peterantypas/maiana/images/Antenna-Example1.jpg

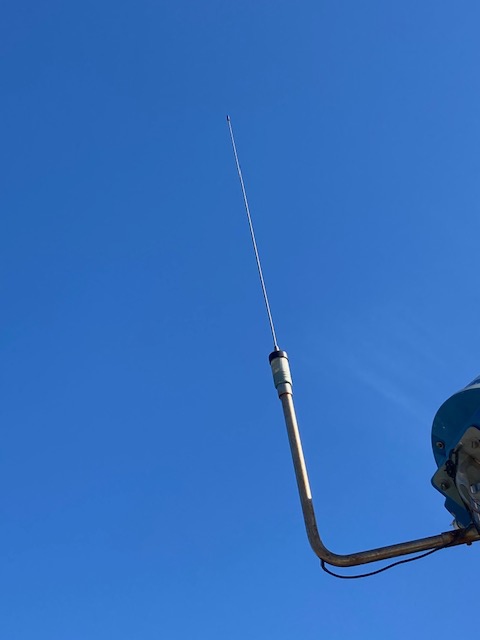
images/Antenna-Example1.jpg
