peterantypas/maiana/images/Antenna-Example3.jpg

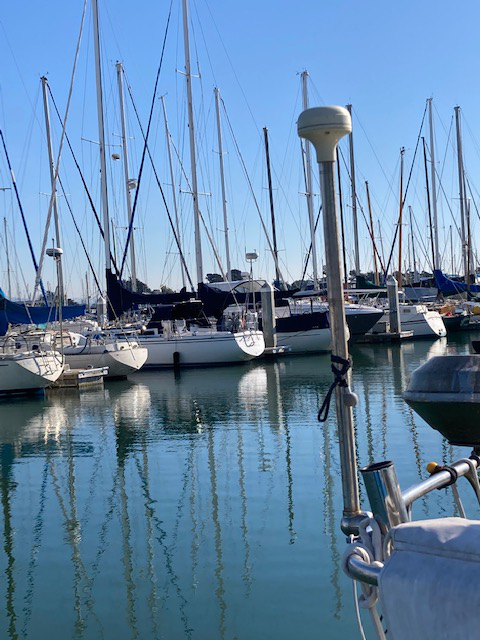
images/Antenna-Example3.jpg
