peterantypas/maiana/images/Board4.3.jpg

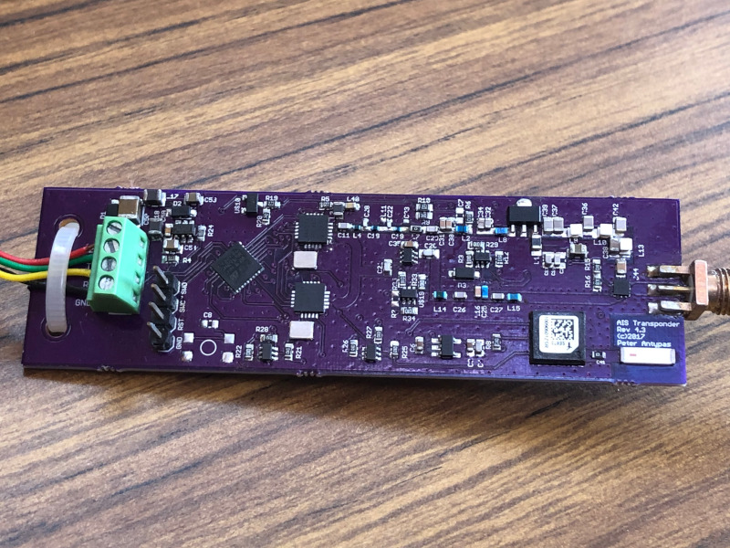
images/Board4.3.jpg
