peterantypas/maiana/images/board-11.3.0.jpg

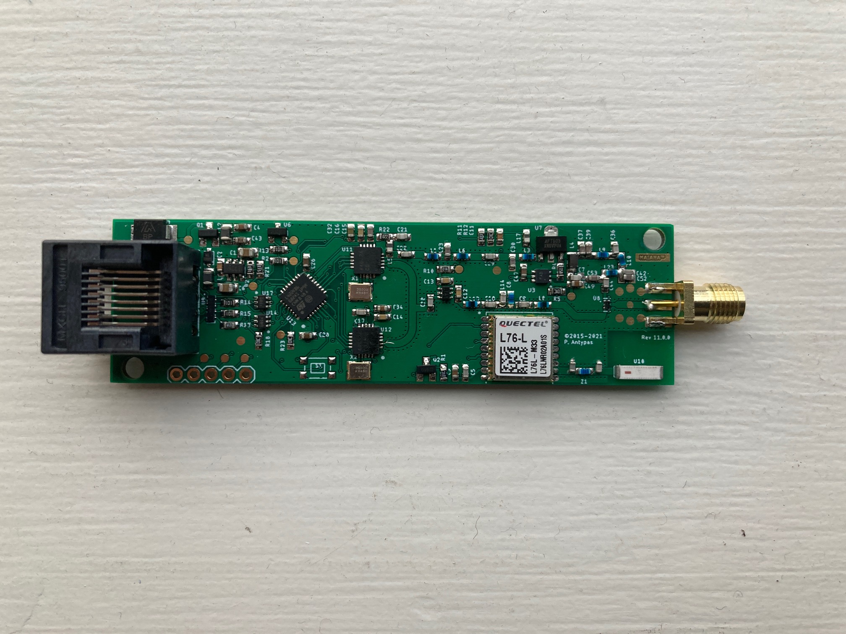
images/board-11.3.0.jpg
