peterantypas/maiana/images/transponder-6.1.jpg

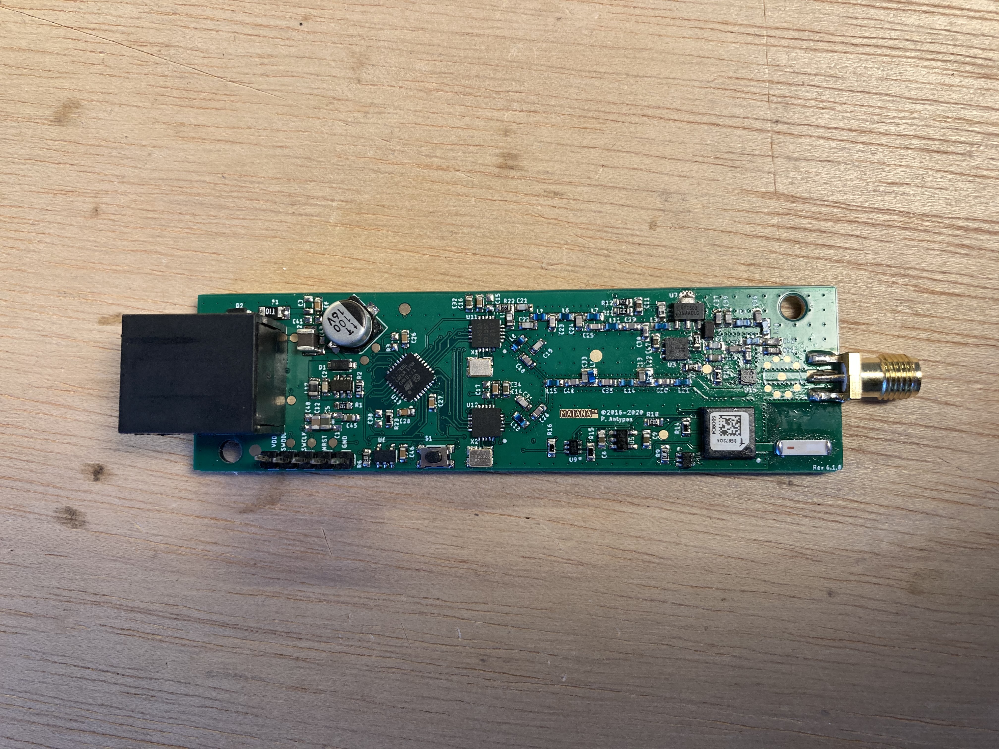
images/transponder-6.1.jpg
