peterantypas/maiana/images/transponder-9.3.jpg

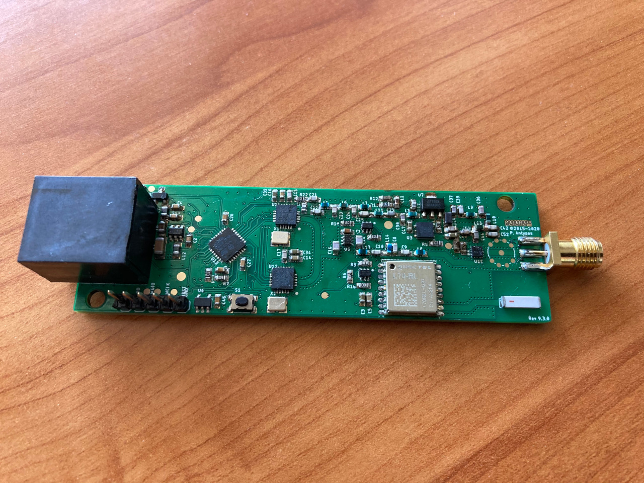
images/transponder-9.3.jpg
