peterantypas/maiana/images/uart_breakout.jpg

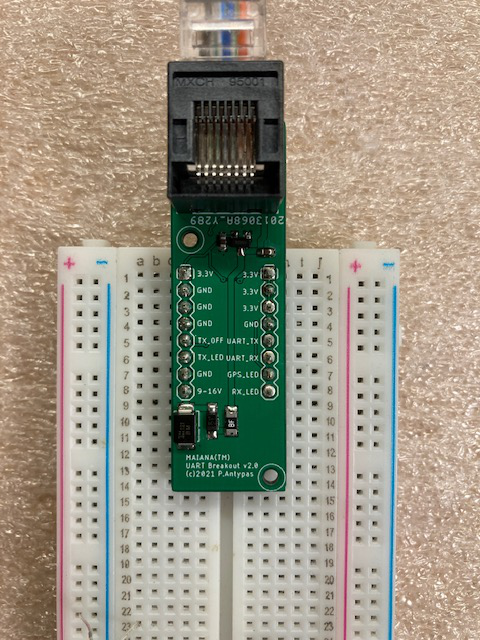
images/uart_breakout.jpg
