peterantypas/maiana/images/usbadapter.jpg

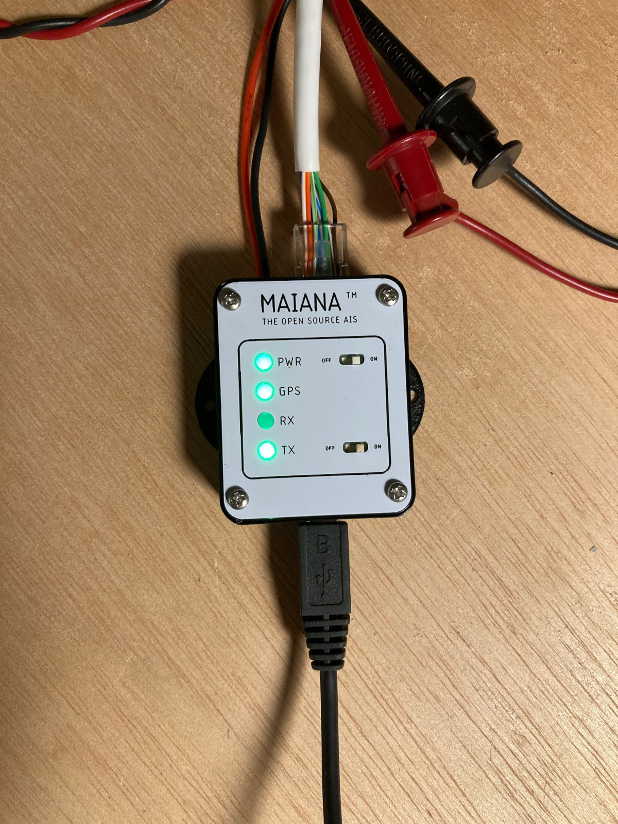
images/usbadapter.jpg
