peterantypas/maiana/latest/CAD/NMEA2000Breakout/n2k-breakout-3.0-ISO-GreenPAK.png

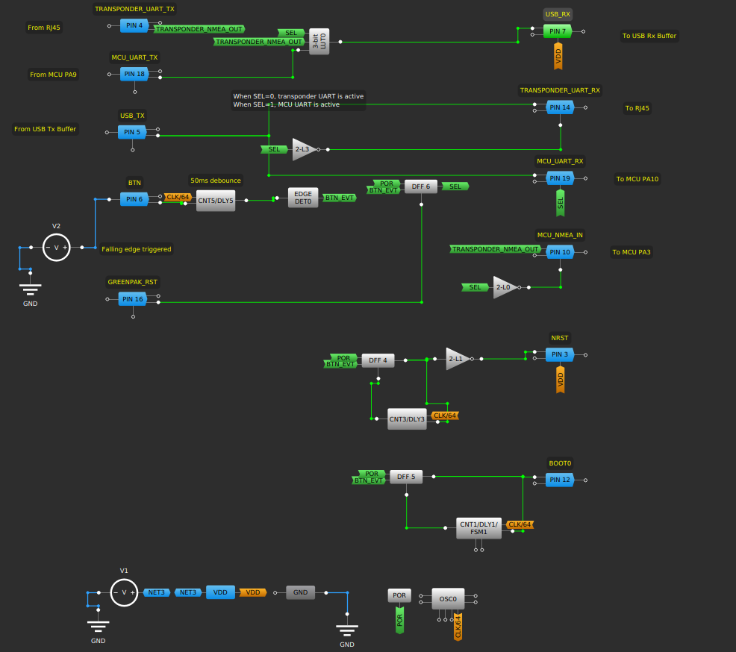
latest/CAD/NMEA2000Breakout/n2k-breakout-3.0-ISO-GreenPAK.png
