peterantypas/maiana/latest/CAD/NMEA2000Breakout/Rev8.1/NMEA2000Adapter-8.1-Schematic.pdf

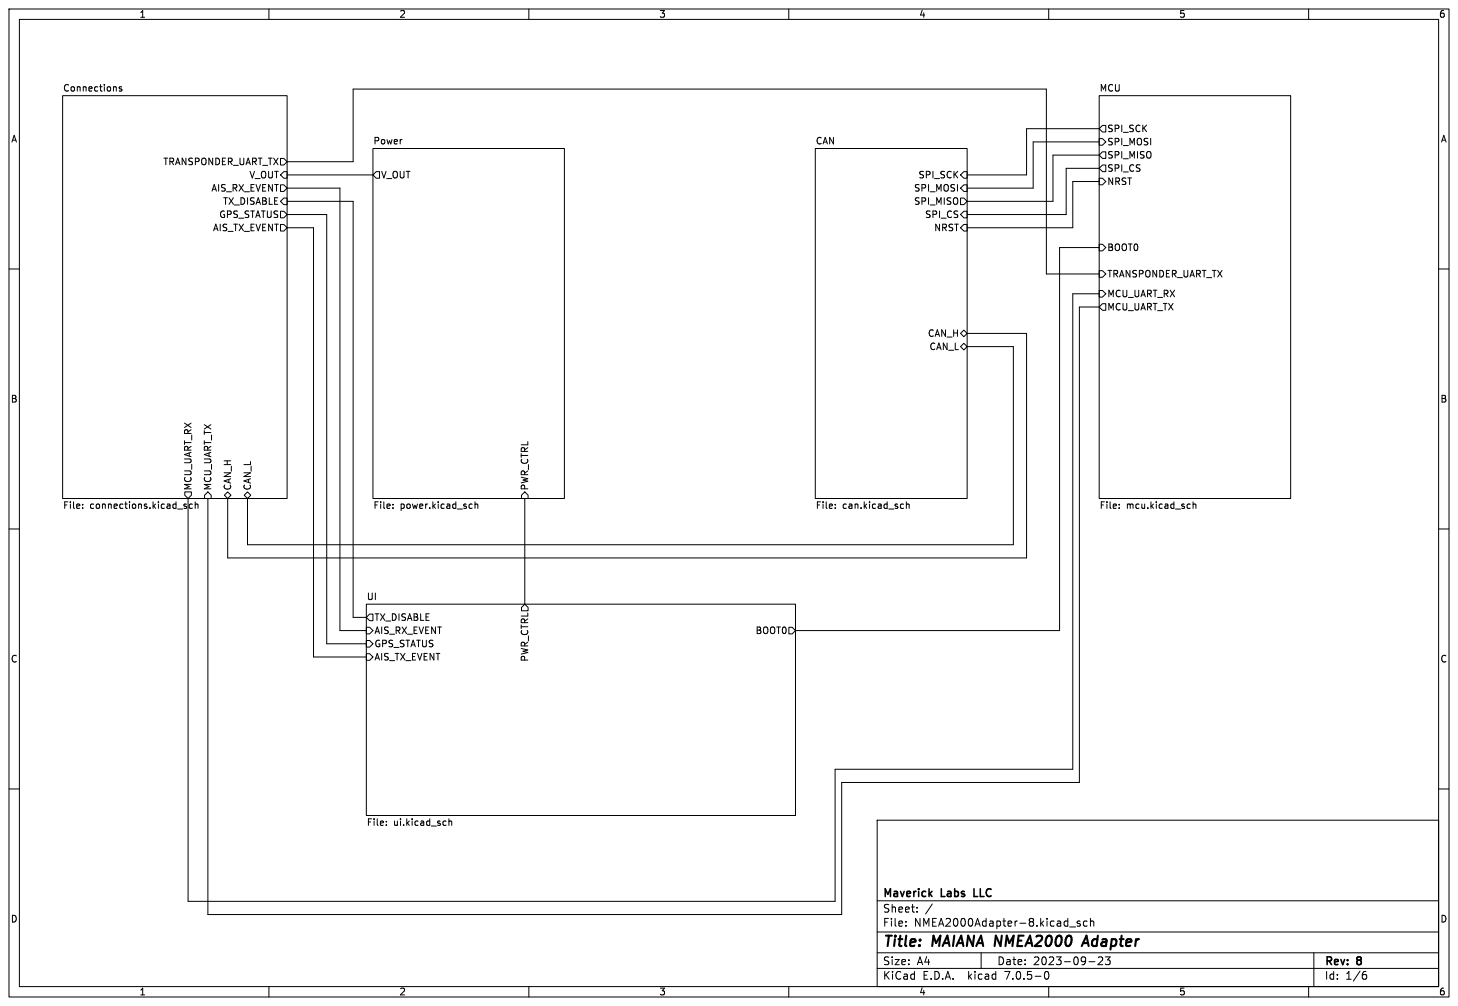
[picture p134: page 1]

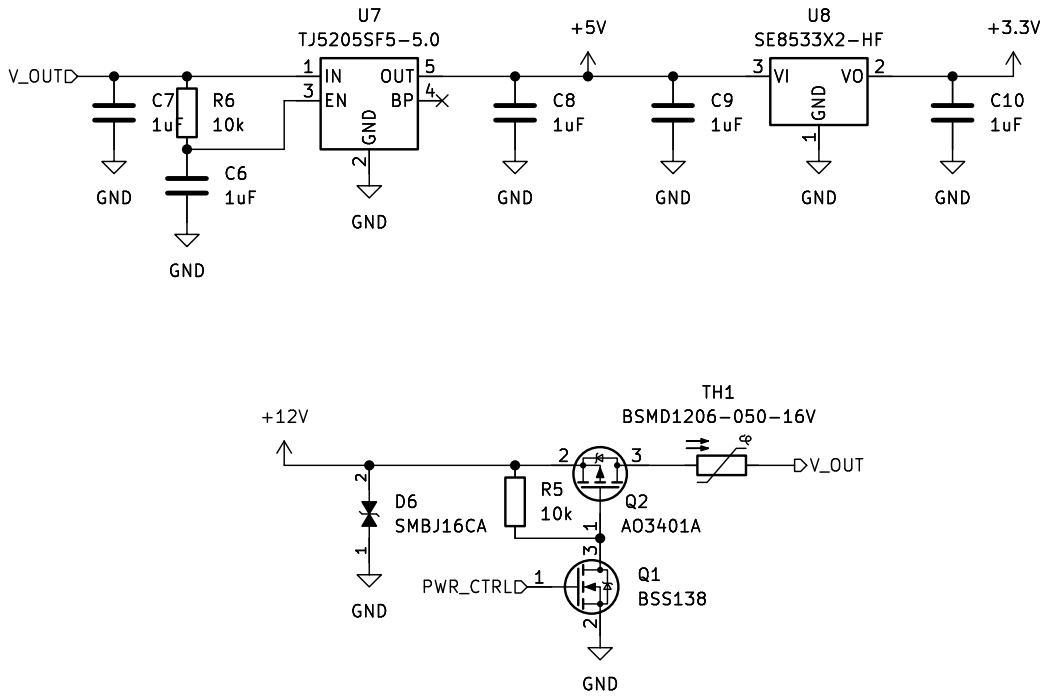
[picture p135: page 2]

2 EN 3 BP 4 OUT 5 U7 TJ5205SF5-5.0 PWR_CTRL V_OUT V_OUT GND Q1 BSS138

1 VO 2 VI 3 U8 SE8533X2-HF GND GND

2 EN 3 BP 4 OUT 5 GND

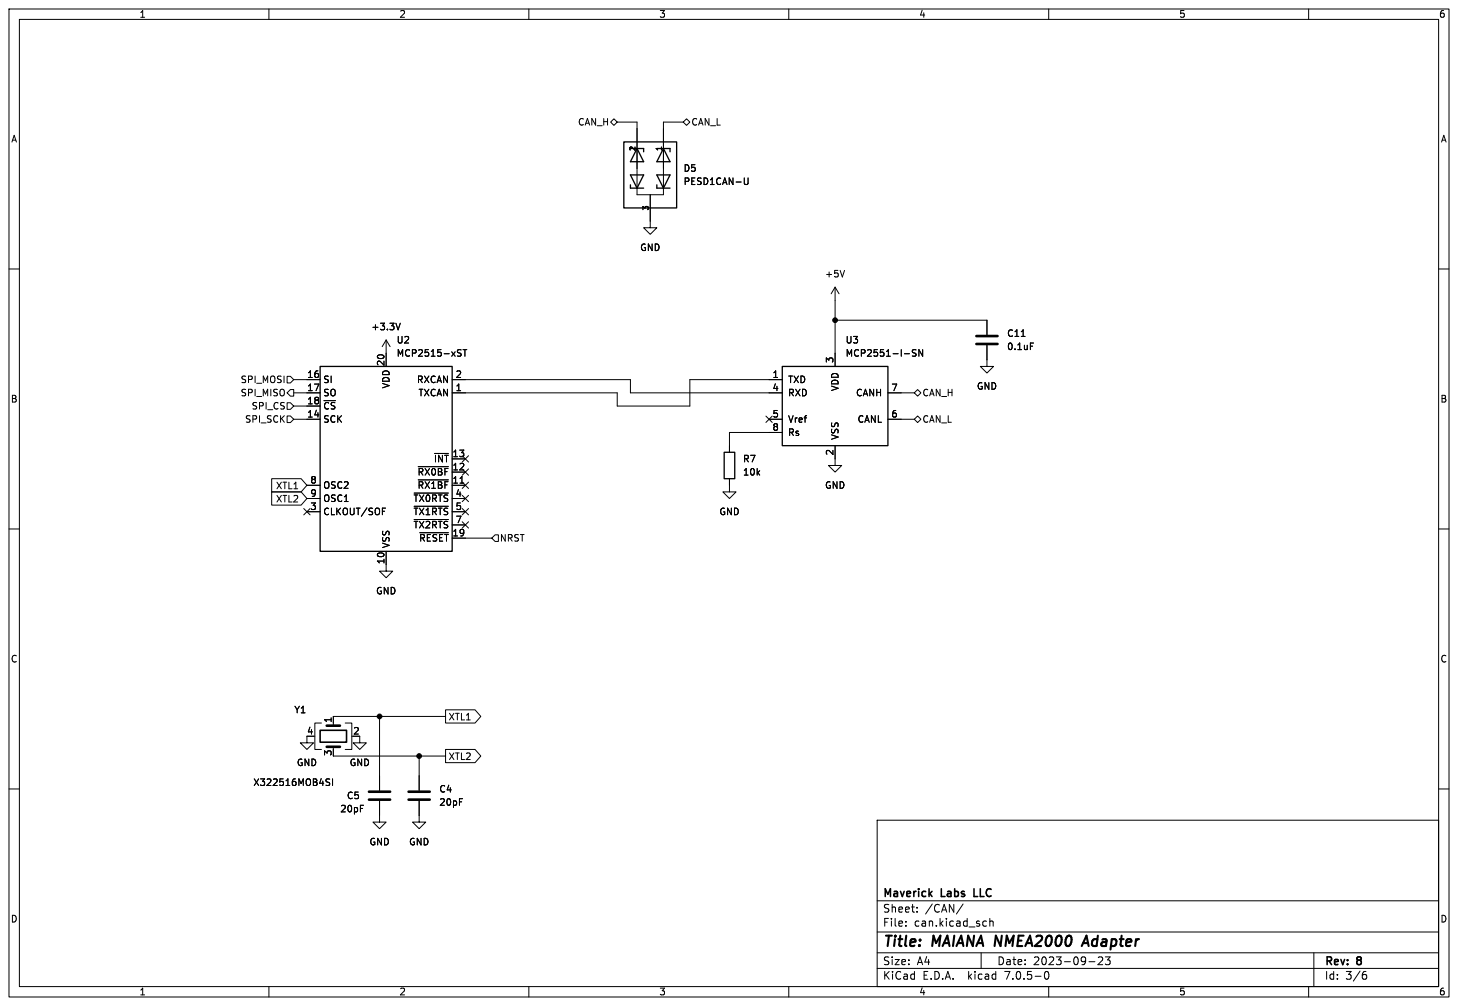
[picture p136: page 3]

3 RXD 4 Vref 5 CANL 6 CANH 7 Rs 8 U3 MCP2551-I-SN

3 RXD 4 Vref 5 CANL 6 CANH 7 Rs 8 GND

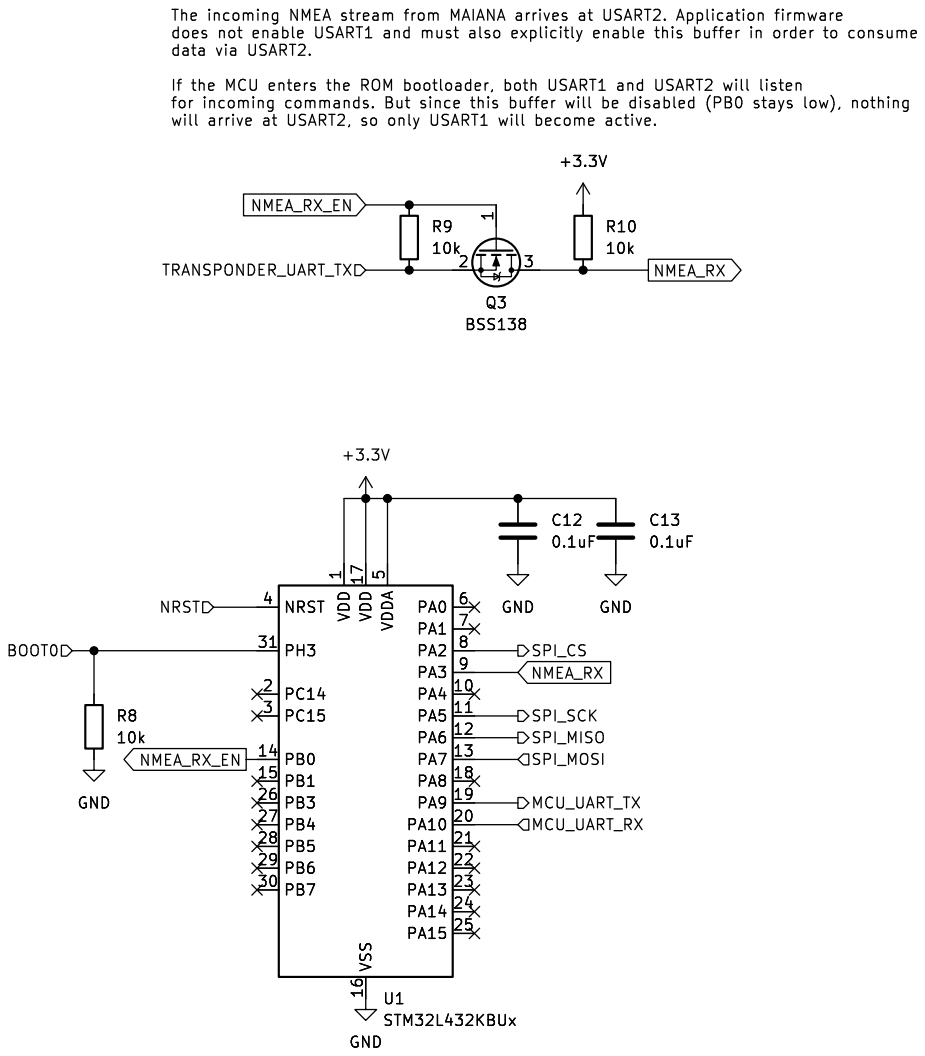
[picture p137: page 4]

1 PA4 10 PA5 11 PA6 12 PA7 13 PB0 14 PB1 15 VSS 16 VDD 17 PA8 18 PA9 19 PC14 2 PA10 20 PA11 21 PA12 22 PA13 23 PA14 24 PA15 25 PB3 26 PB4 27 PB5 28 PB6 29 PC15 3 PB7 30 PH3 31 NRST 4 VDDA

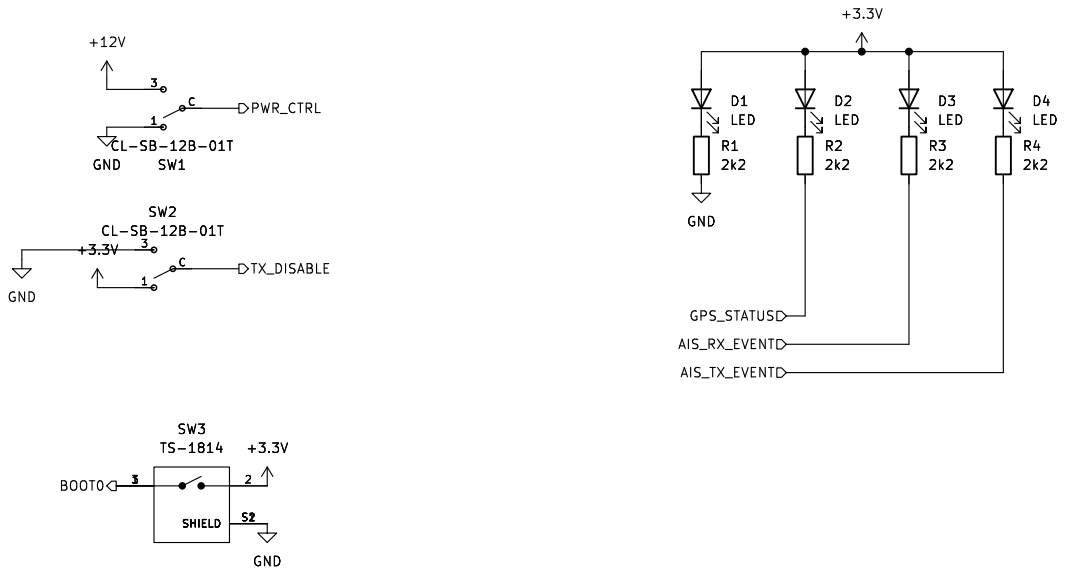
[picture p138: page 5]

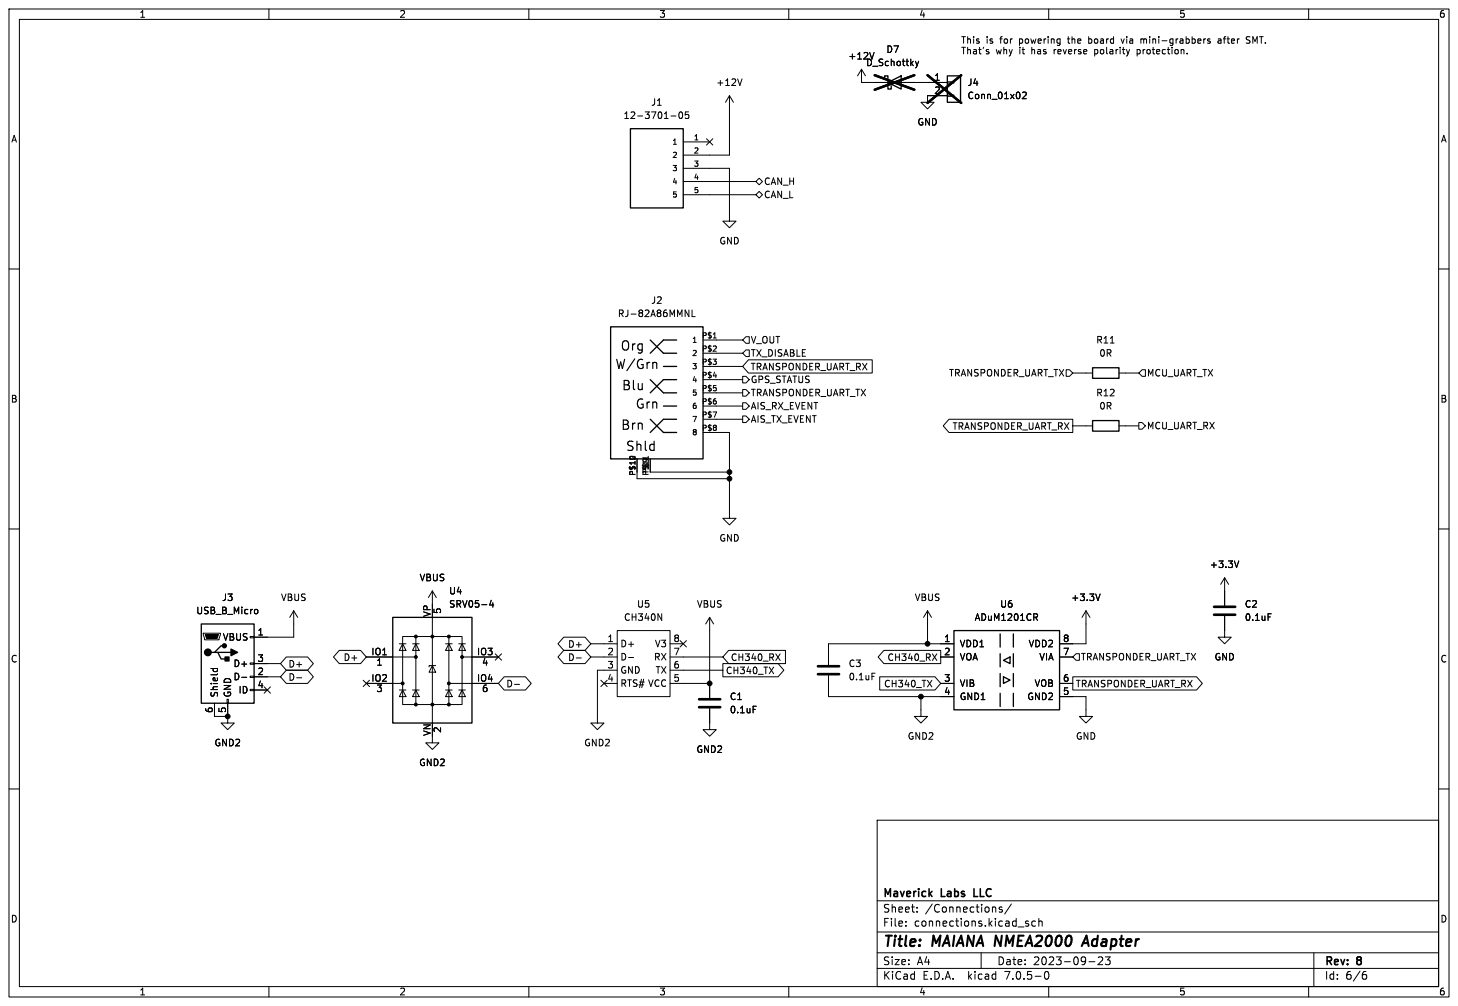
[picture p139: page 6]
