peterantypas/maiana/eagle/rf.sch.pdf

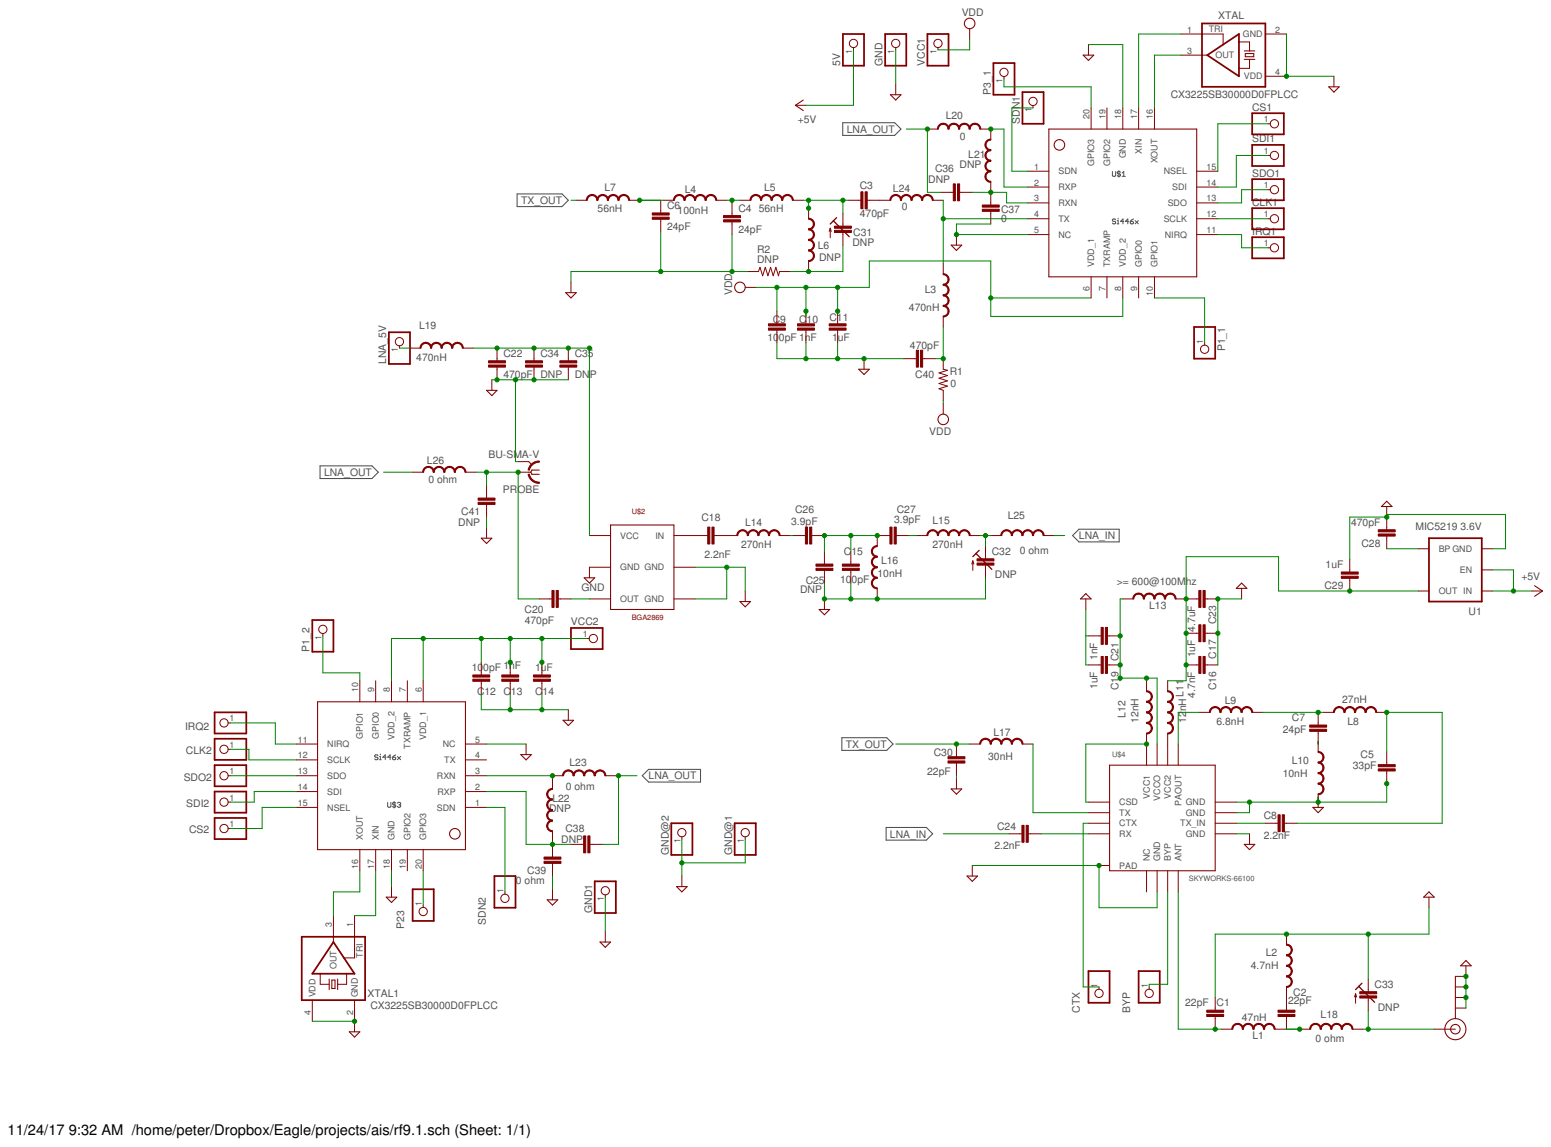
[picture p140: page 1]

IN GND OUT EN

GND OUT GND GND
GND

11/24/17 9:32 AM /home/peter/Dropbox/Eagle/projects/ais/rf9.1.sch (Sheet: 1/1)
