peterantypas/maiana/latest/CAD/UARTBreakout/UARTBreakout-3.0-schemetic.pdf

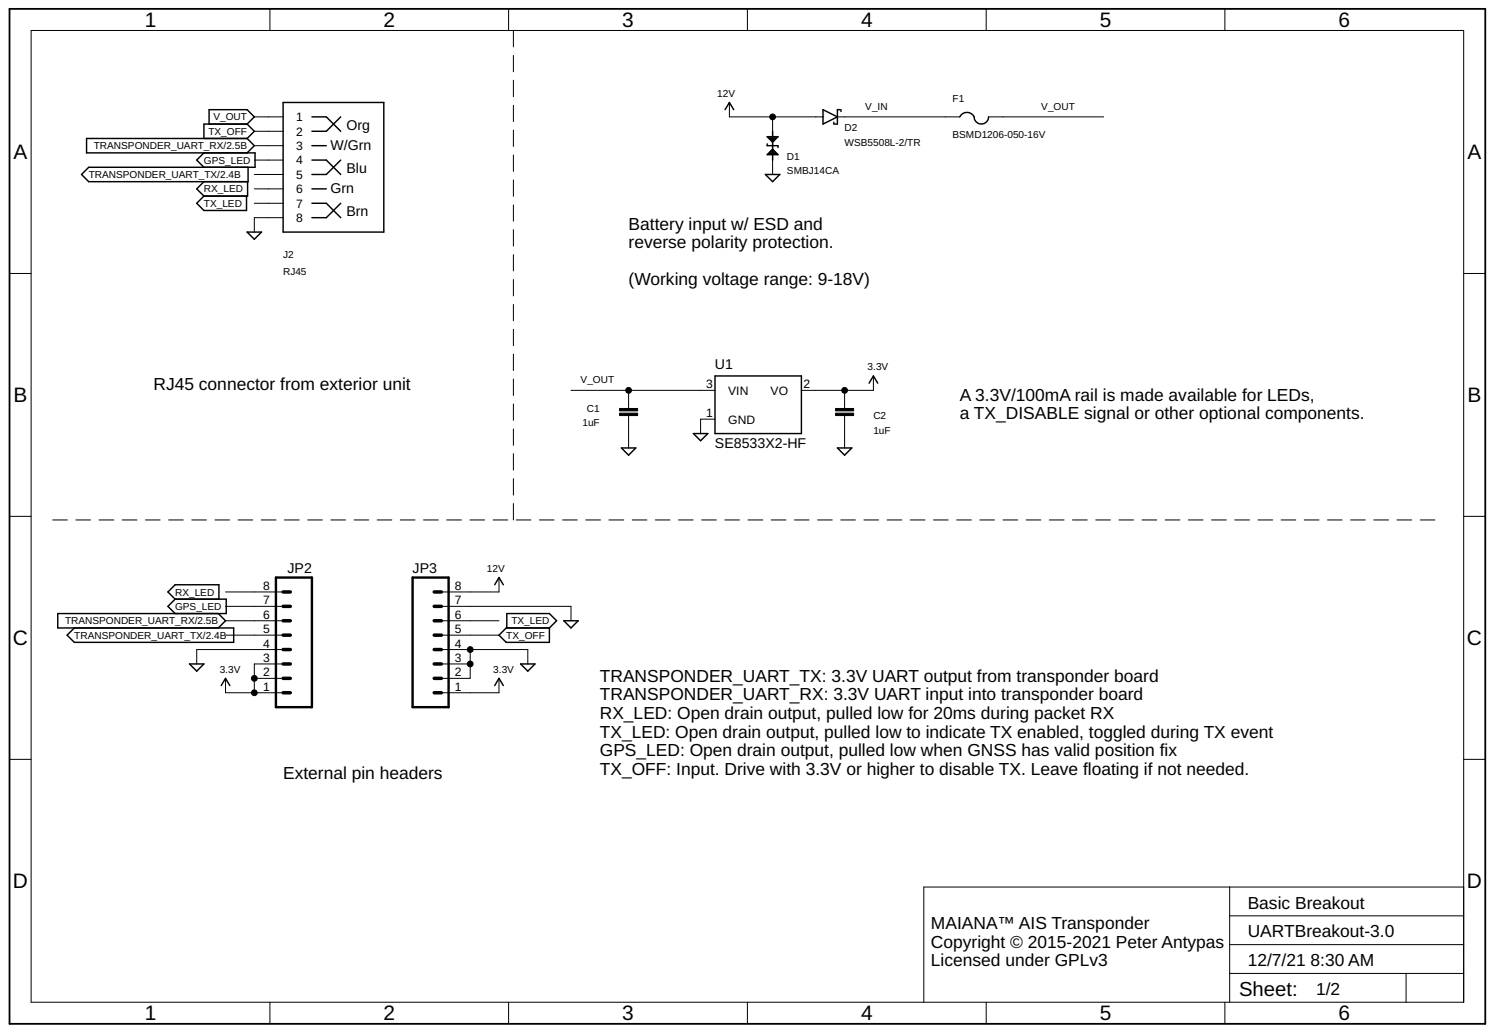
[picture p141: page 1]

Battery input w/ ESD and
reverse polarity protection. (Working voltage range: 9-18V)

RJ45 connector from exterior unit

A 3.3V/100mA rail is made available for LEDs, a TX_DISABLE signal or other optional components.

TRANSPONDER_UART_TX: 3.3V UART output from transponder board
TRANSPONDER_UART_RX: 3.3V UART input into transponder board
RX_LED: Open drain output, pulled low for 20ms during packet RX
TX_LED: Open drain output, pulled low to indicate TX enabled, toggled during TX event
GPS_LED: Open drain output, pulled low when GNSS has valid position fix
TX_OFF: Input. Drive with 3.3V or higher to disable TX. Leave floating if not needed.

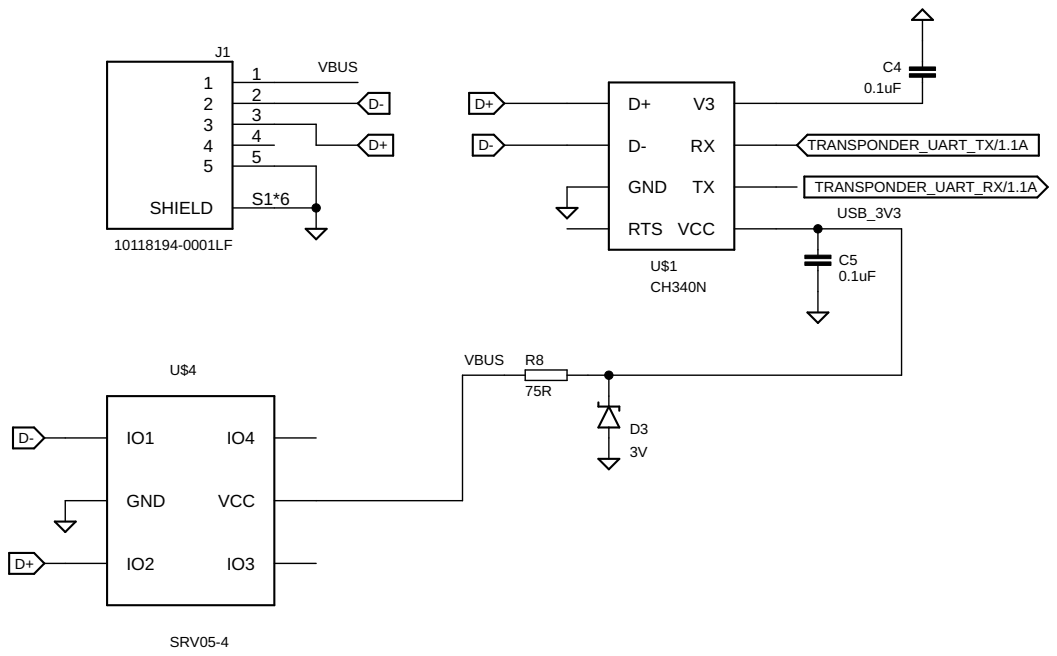
[picture p142: page 2]
