peterantypas/maiana/latest/CAD/Board-11.9/transponder-11.9.1/transponder-11.9.1.pdf

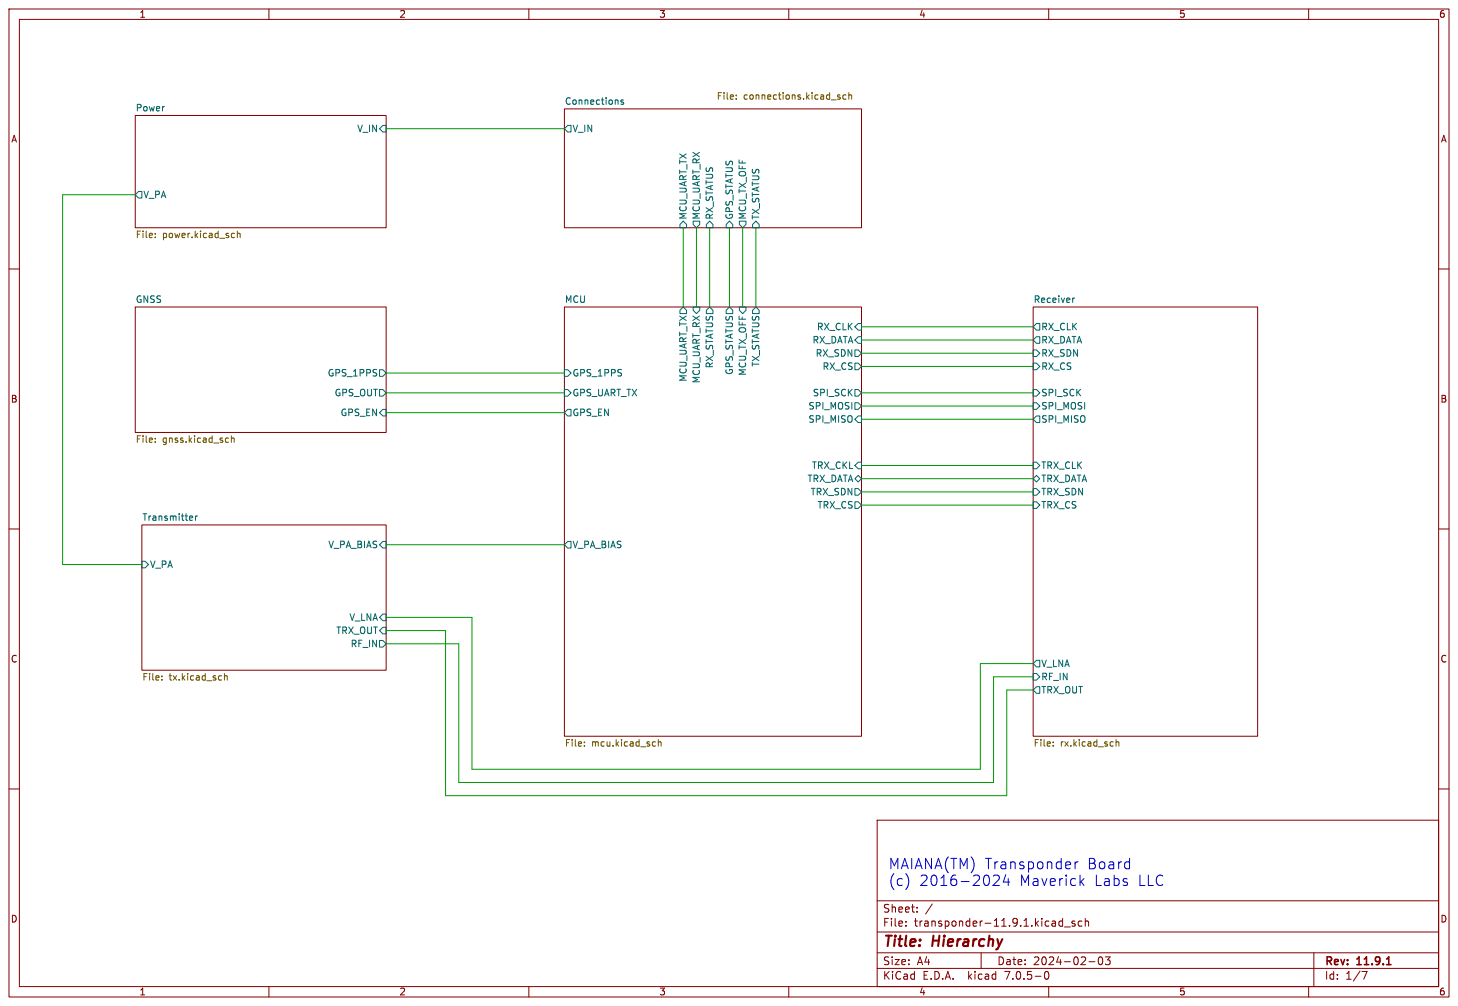
[picture p143: page 1]

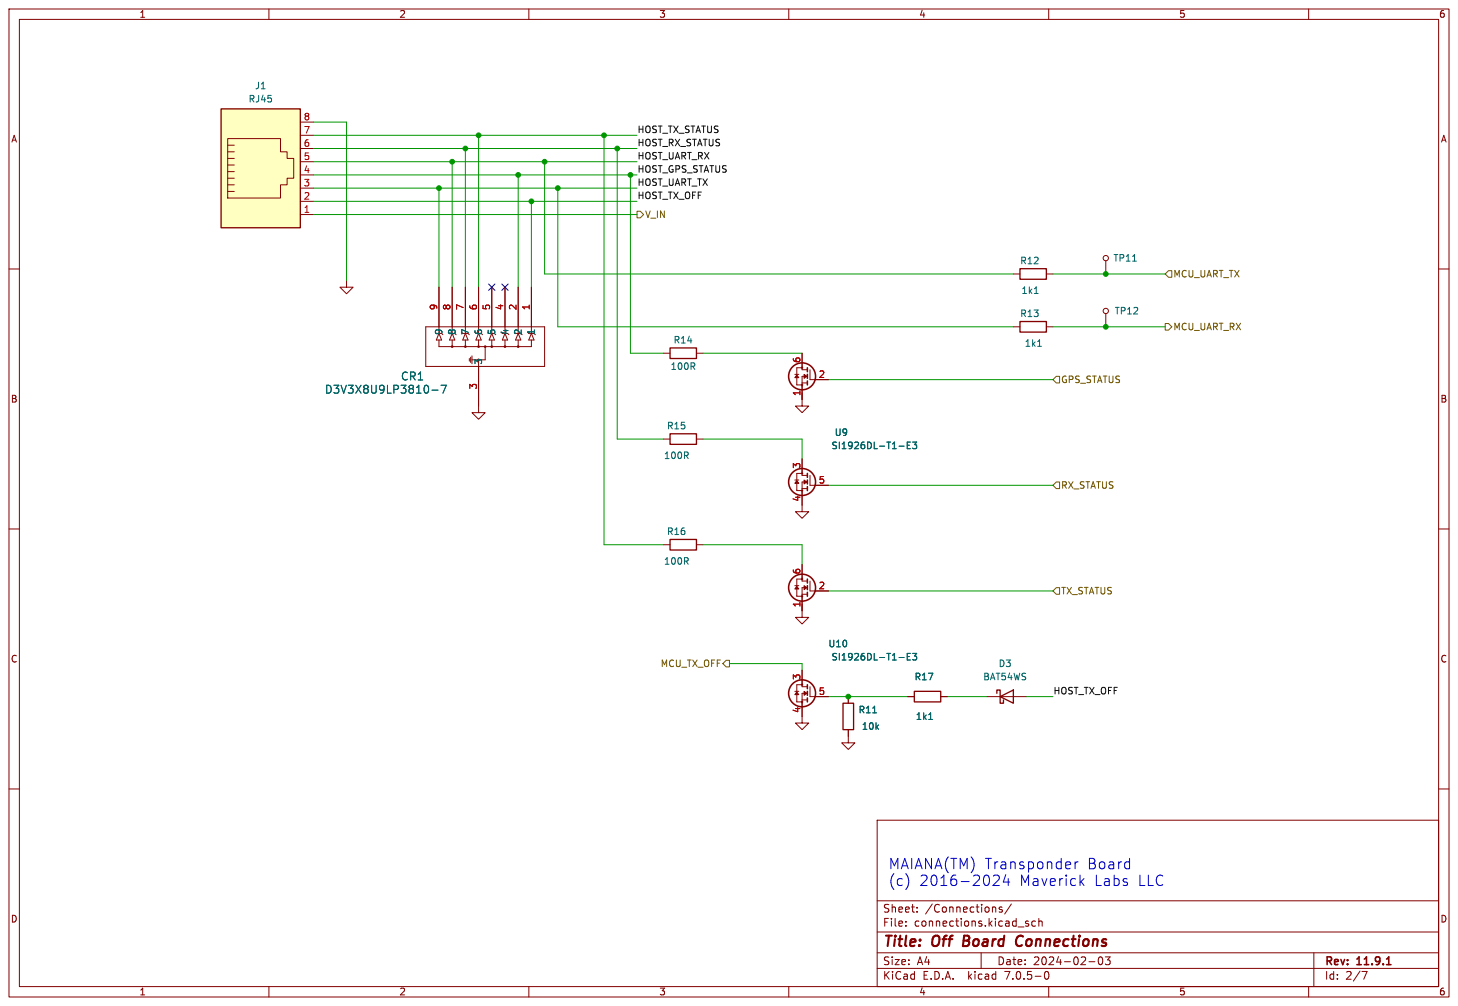
[picture p144: page 2]

File: connections.kicad_sch Sheet: /Connections/
Id: 2/7 Title: Off Board Connections

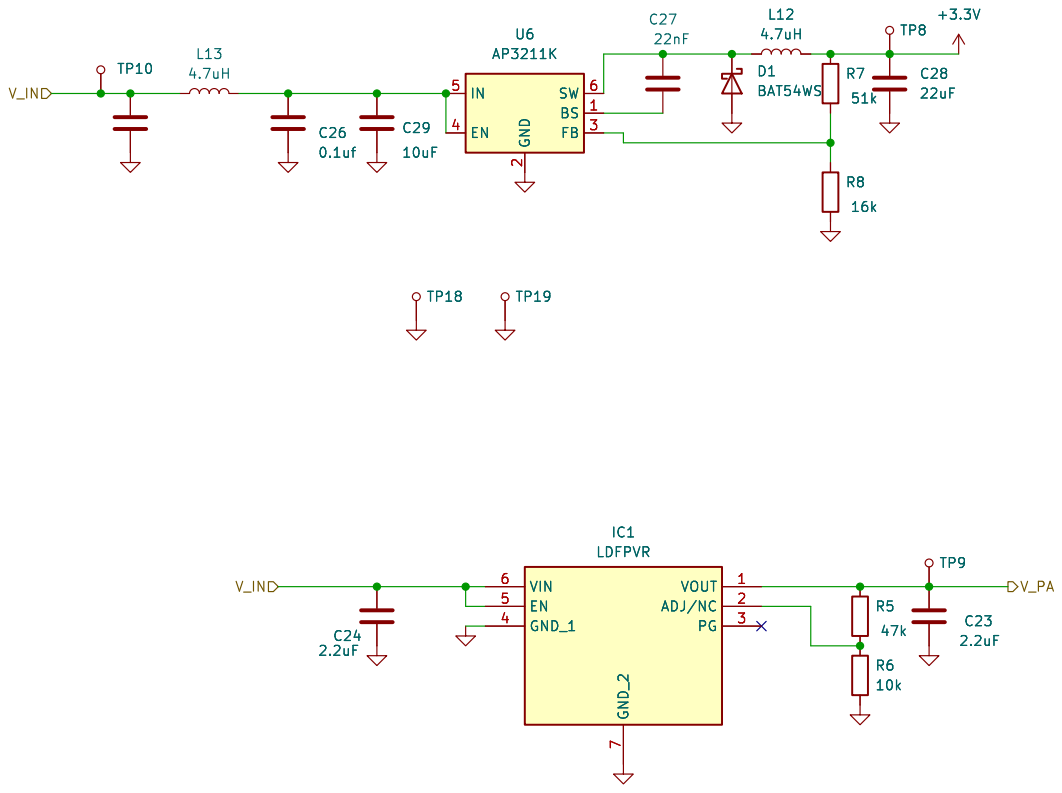
[picture p145: page 3]

File: power.kicad_sch Sheet: /Power/
Id: 3/7 Title: Power Supply

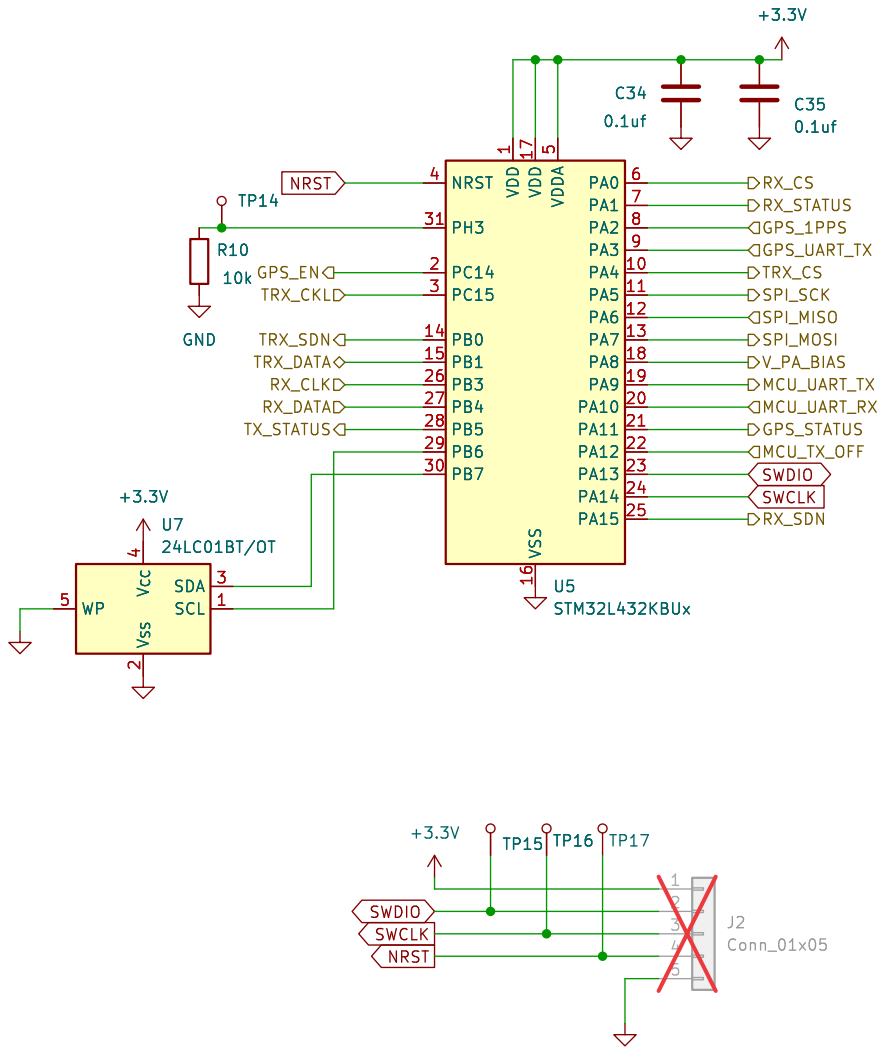
[picture p146: page 4]

1 PA4 10 PA5 11 PA6 12 PA7 13 PB0 14 PB1 15 VSS 16 VDD 17 PA8 18 PA9 19 PC14 2 PA10 20 PA11 21 PA12 22 PA13 23 PA14 24 PA15 25 PB3 26 PB4 27 PB5 28 PB6 29 PC15 3 PB7 30 PH3 31 NRST 4 VDDA

File: mcu.kicad_sch Sheet: /MCU/ TP16 +3.3V

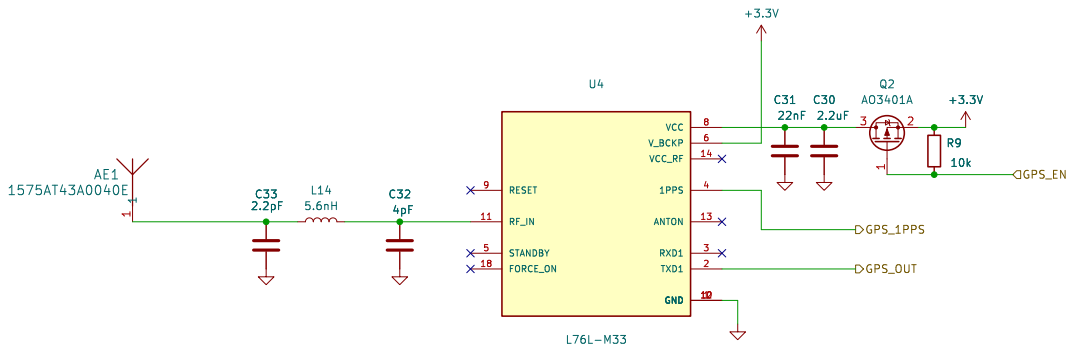
[picture p147: page 5]

File: gnss.kicad_sch Sheet: /GNSS/
Id: 5/7 Title: GNSS

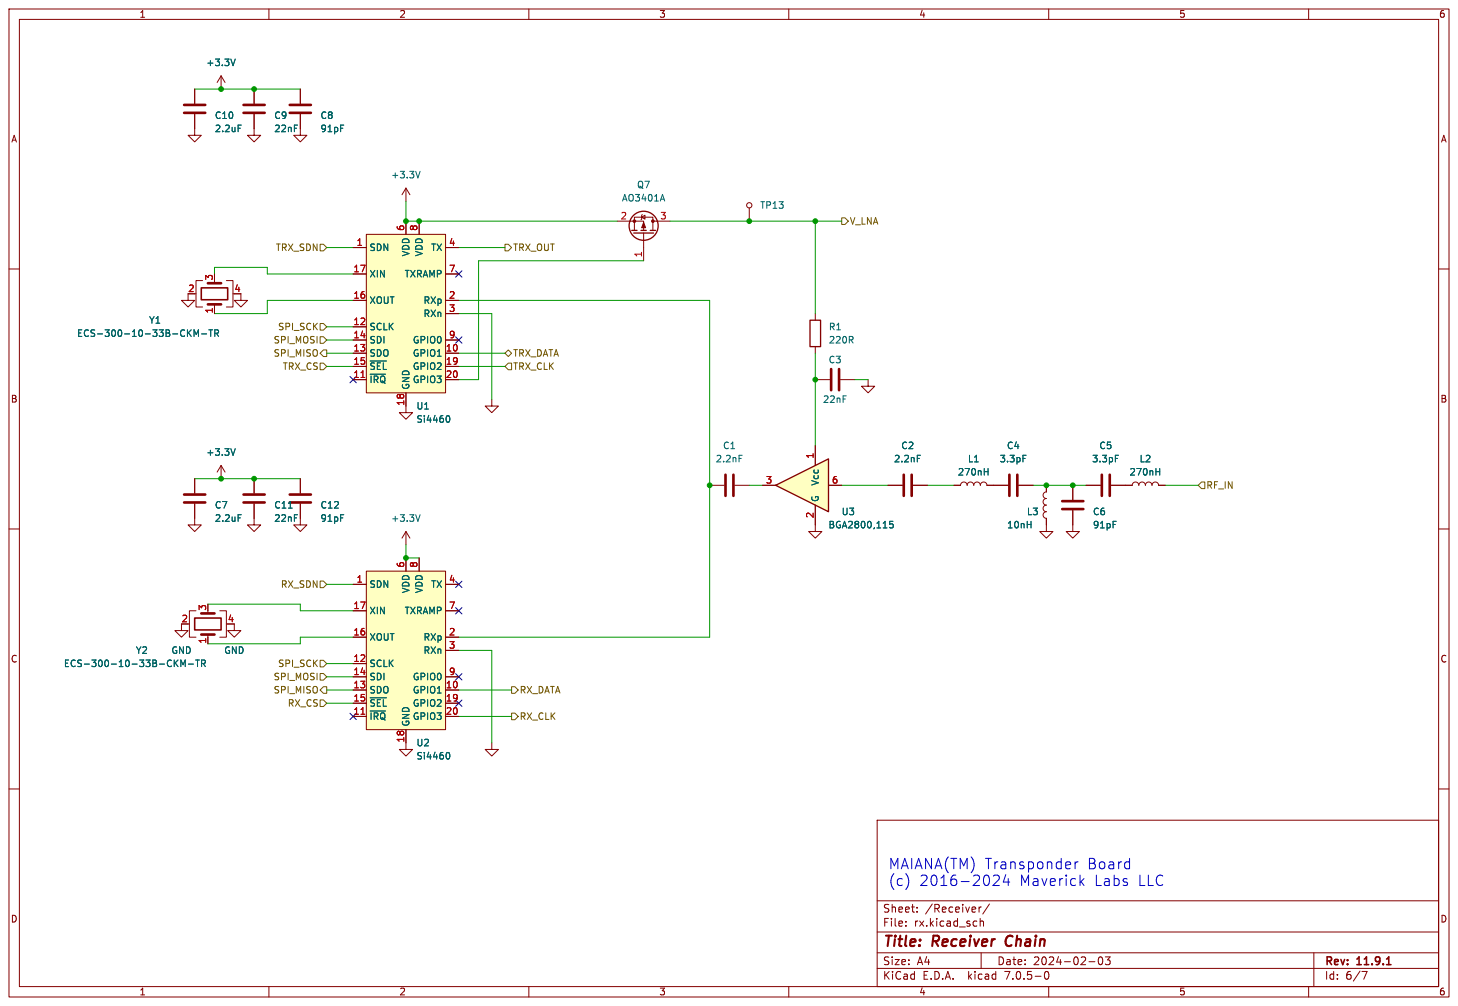
[picture p148: page 6]

8 GPIO0 9 U2Si4460 SDN 1 GPIO1 10 ~{IRQ} 11 SCLK 12 SDO 13 SDI 14 ~{SEL} 15 XOUT 16 XIN 17 GND 18 GPIO2 19 RXp 2 GPIO3 20 RXn 3 TX 4 VDD

File: rx.kicad_sch Sheet: /Receiver/
Id: 6/7 Title: Receiver Chain

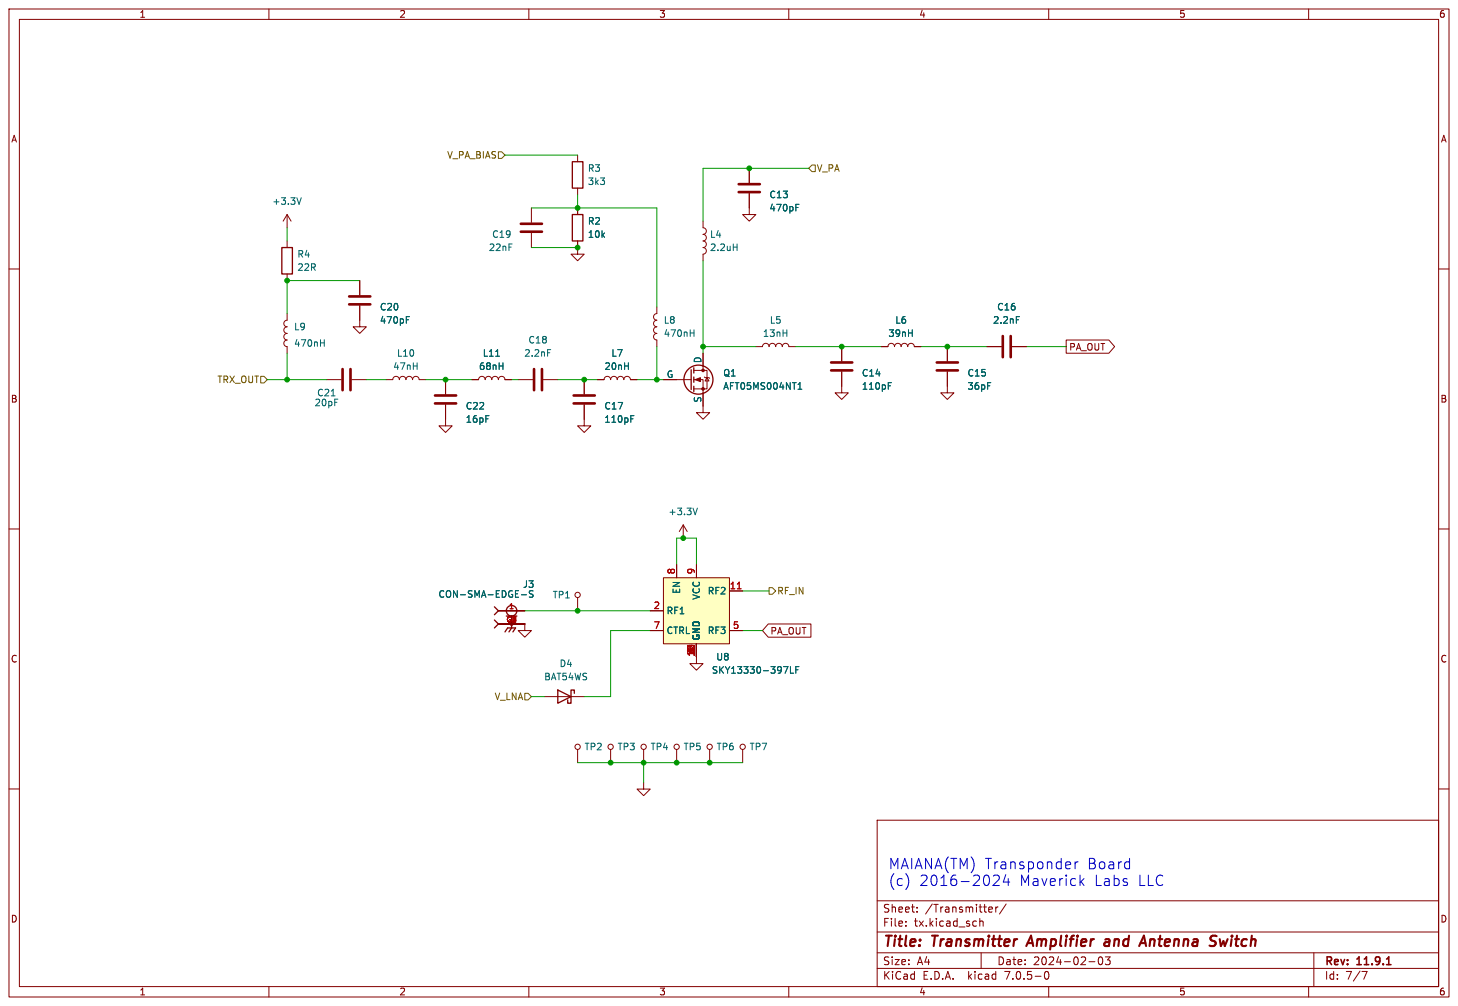
[picture p149: page 7]

File: tx.kicad_sch Sheet: /Transmitter/
Id: 7/7 Title: Transmitter Amplifier and Antenna Switch
