peterantypas/maiana/latest/CAD/Board-10.5/rj45-breakout-10.5.0-schematic.pdf

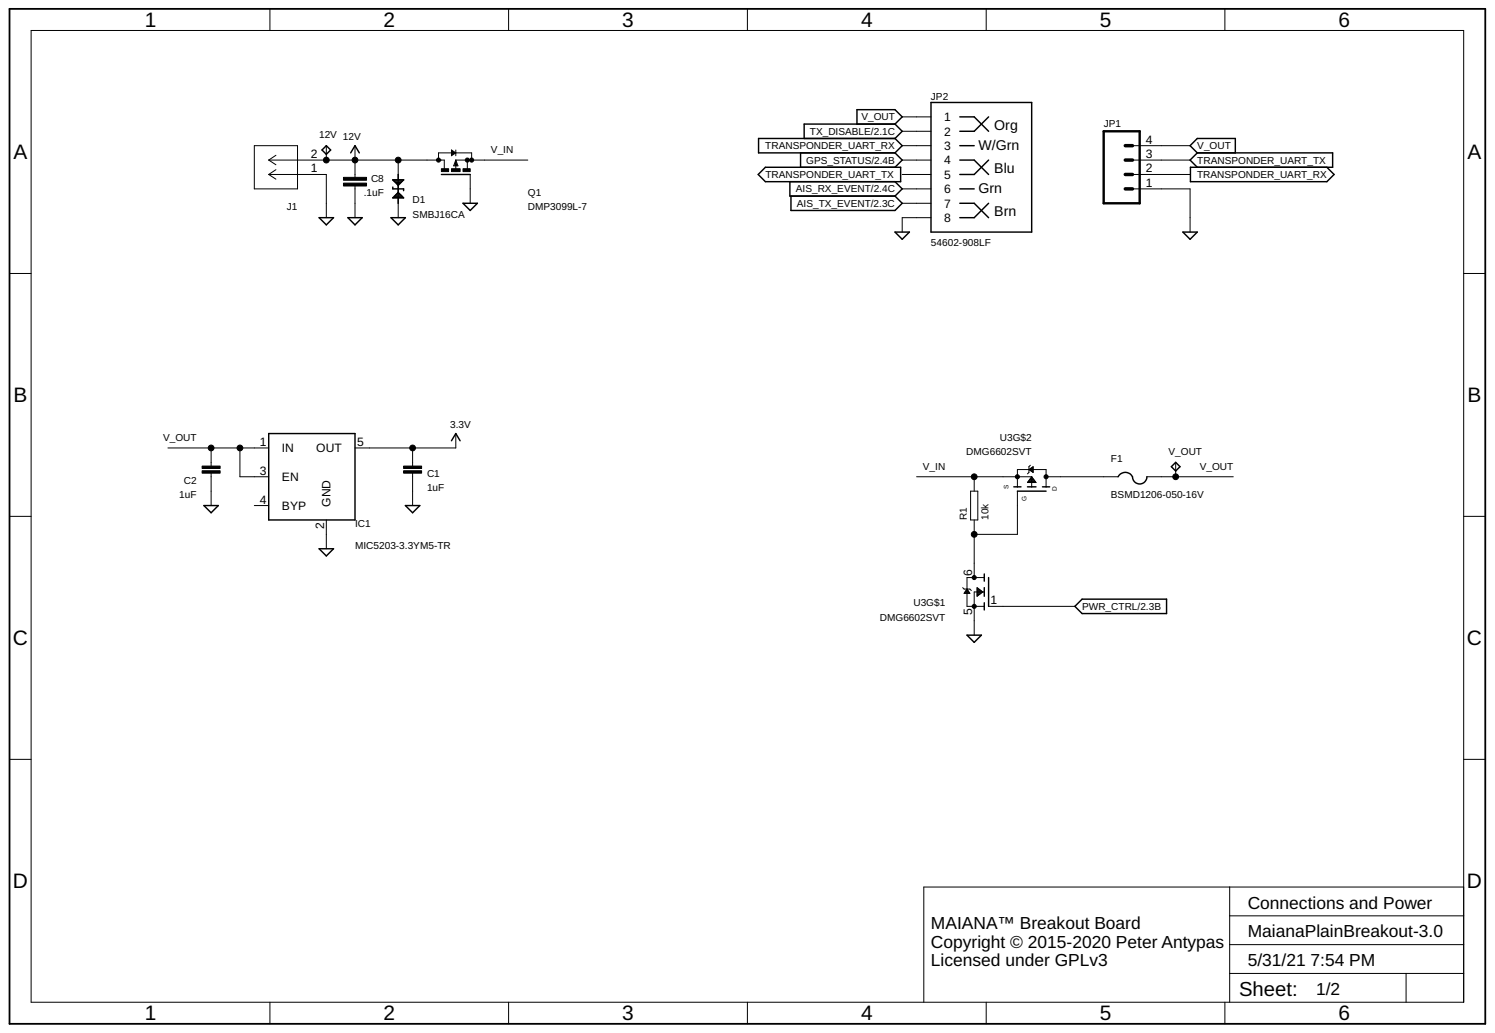
[picture p150: page 1]

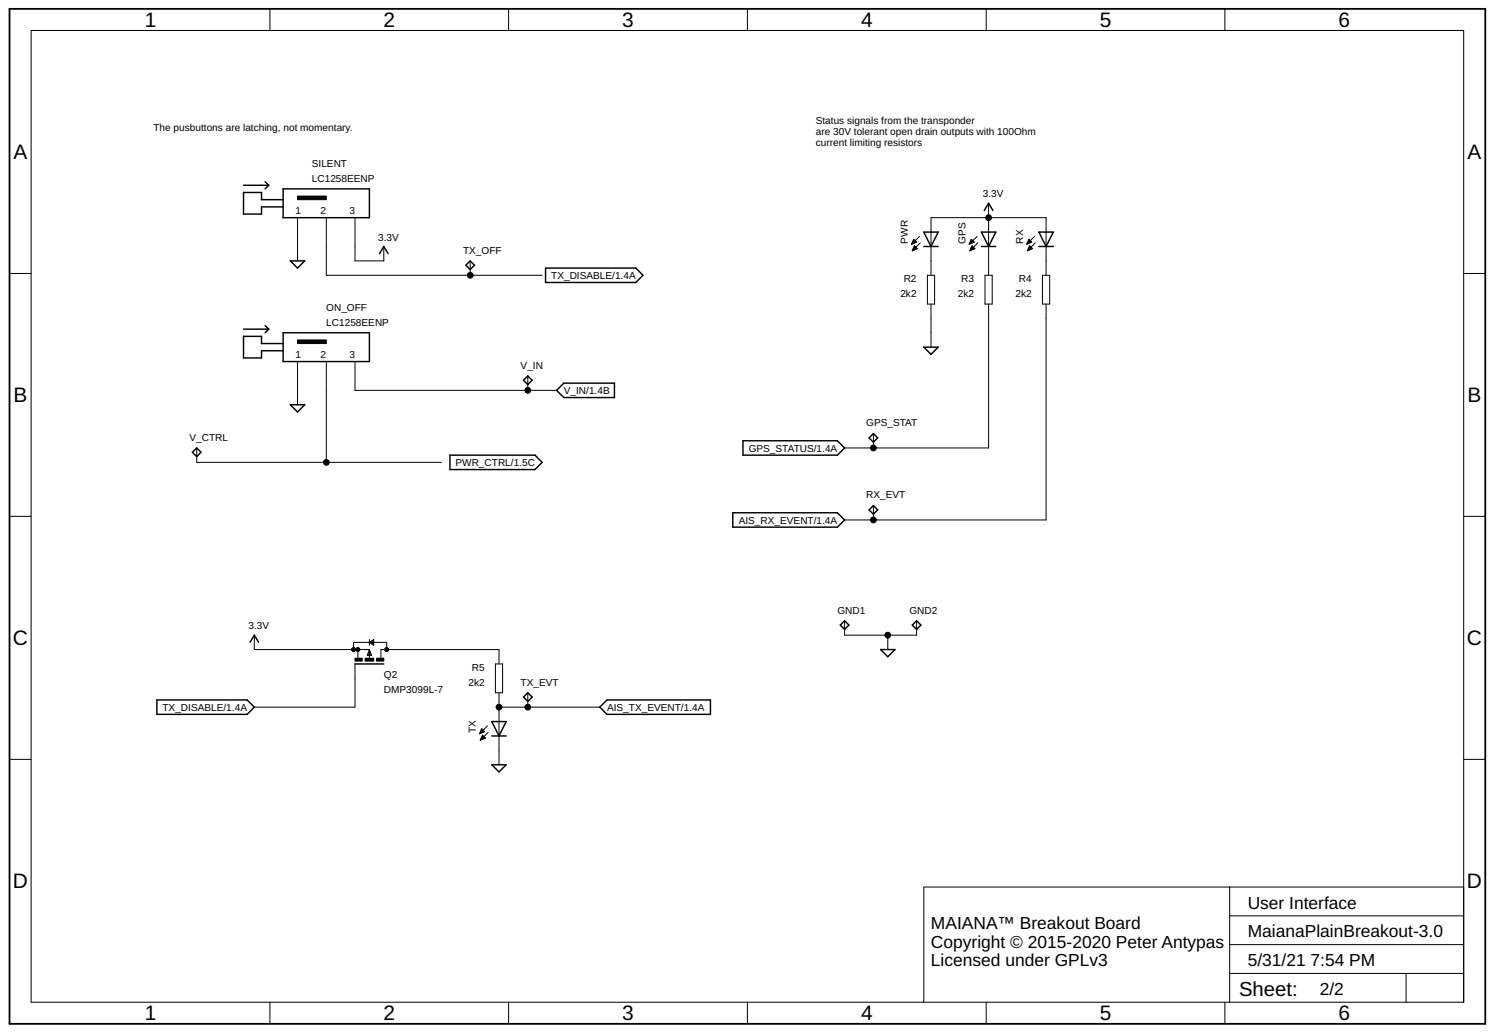
[picture p151: page 2]
