peterantypas/maiana/latest/CAD/Board-10.0/rj45-breakout-10.0.x-schematic.pdf

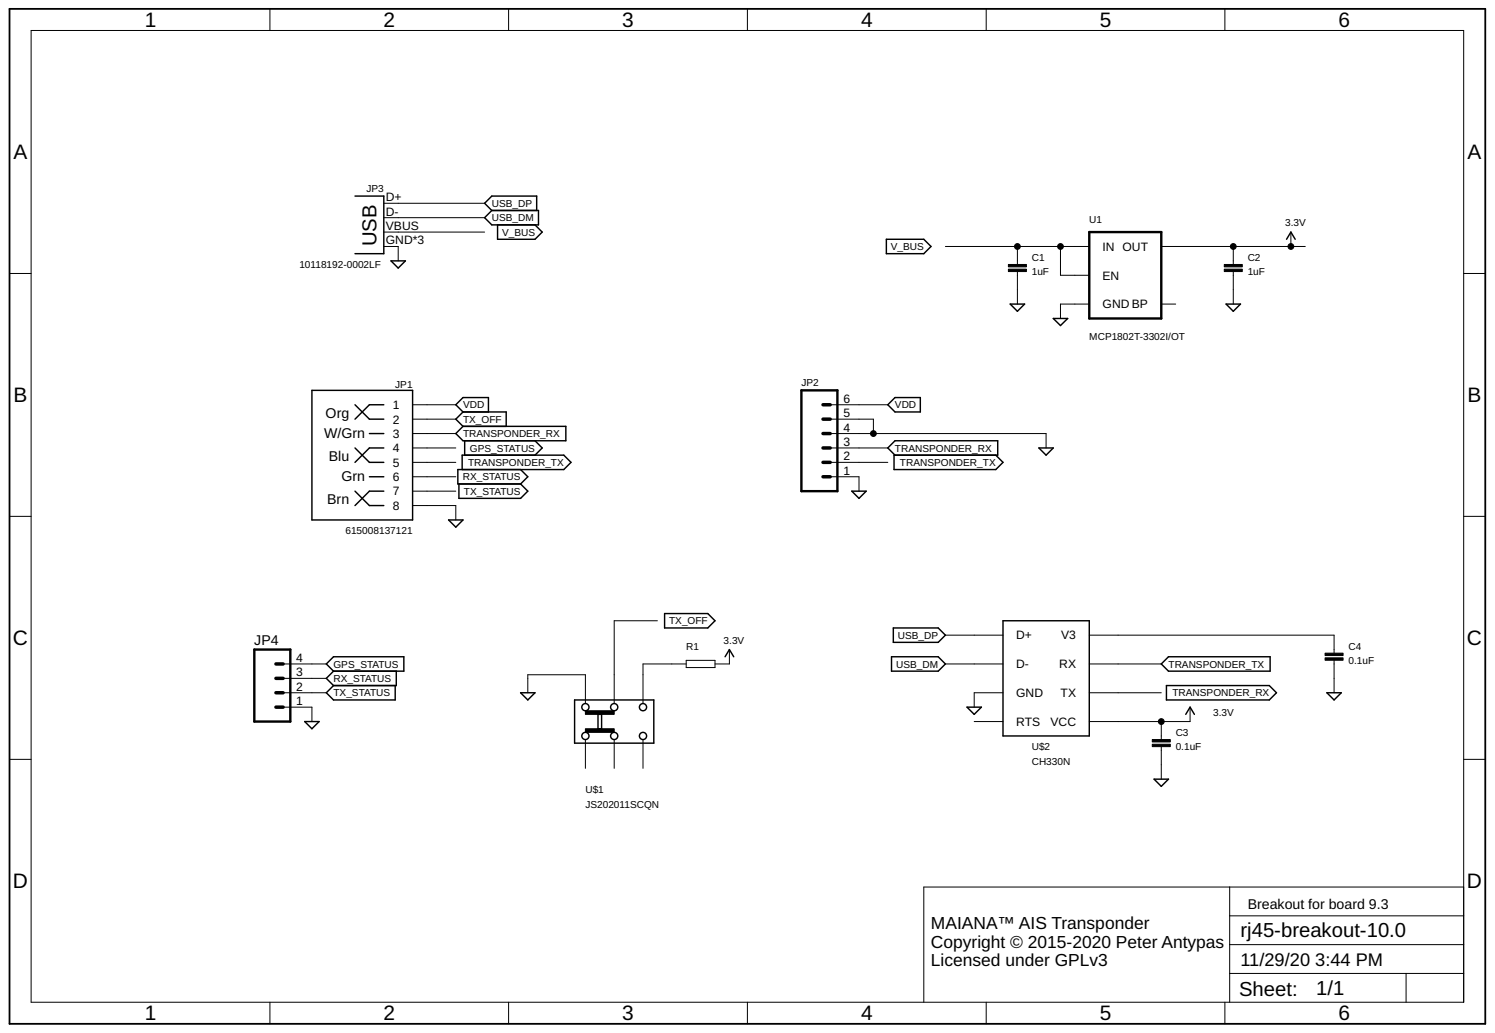
[picture p152: page 1]
