peterantypas/maiana/latest/CAD/Board-9.3/rj45-breakout-9.3-schematic.pdf

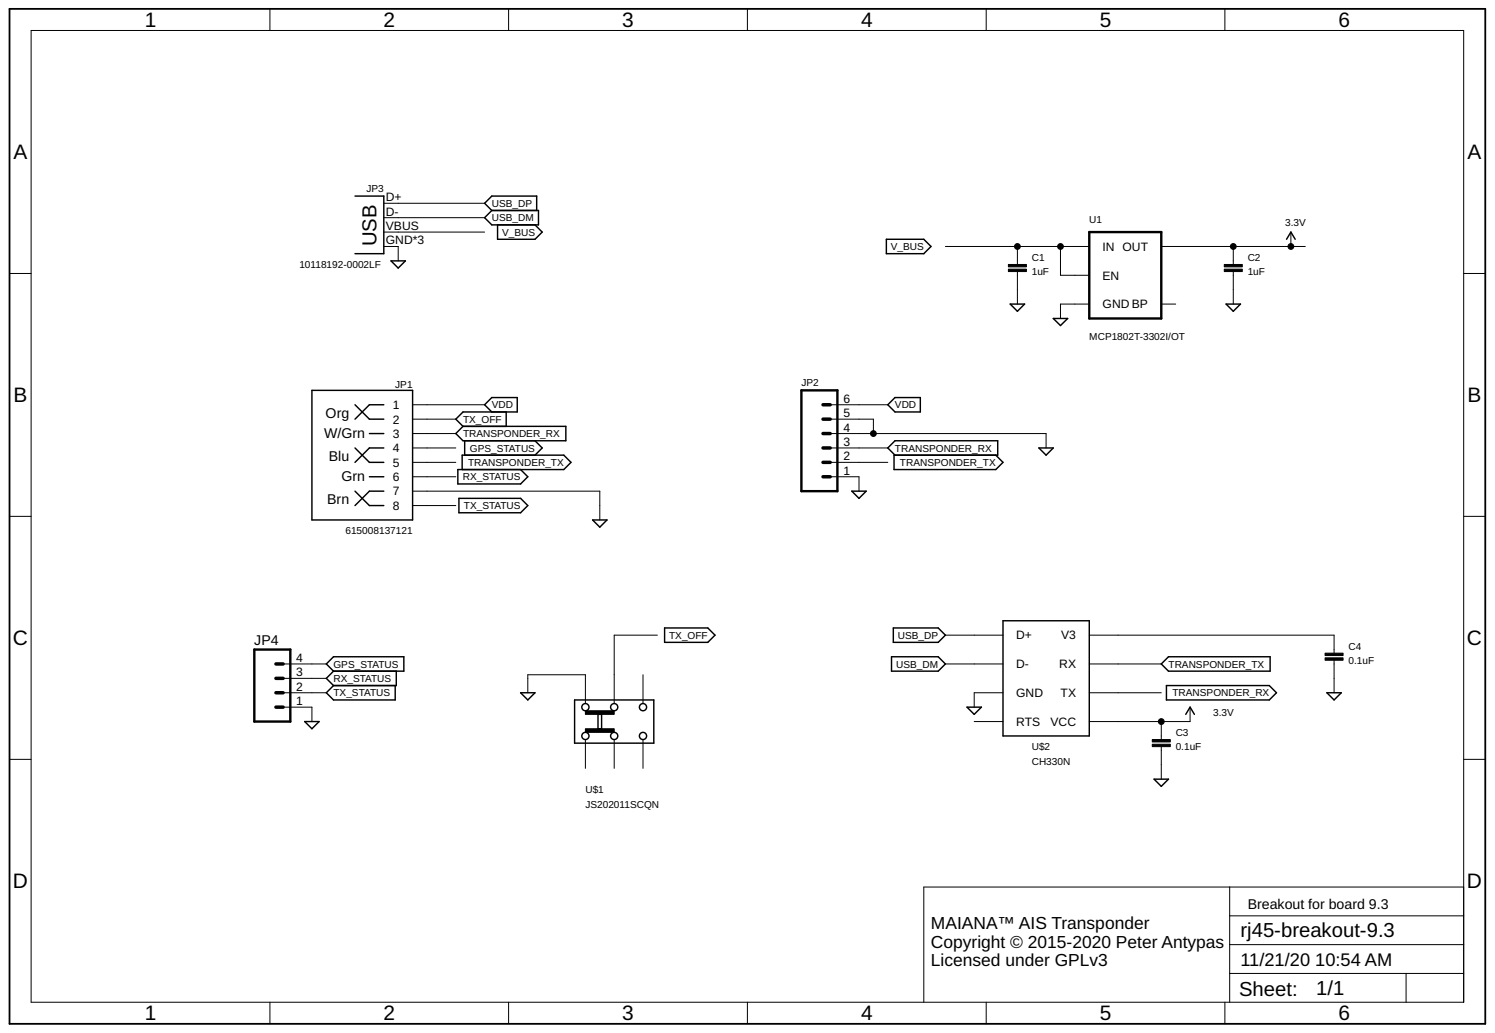
[picture p153: page 1]
