peterantypas/maiana/eagle/logic.sch.pdf

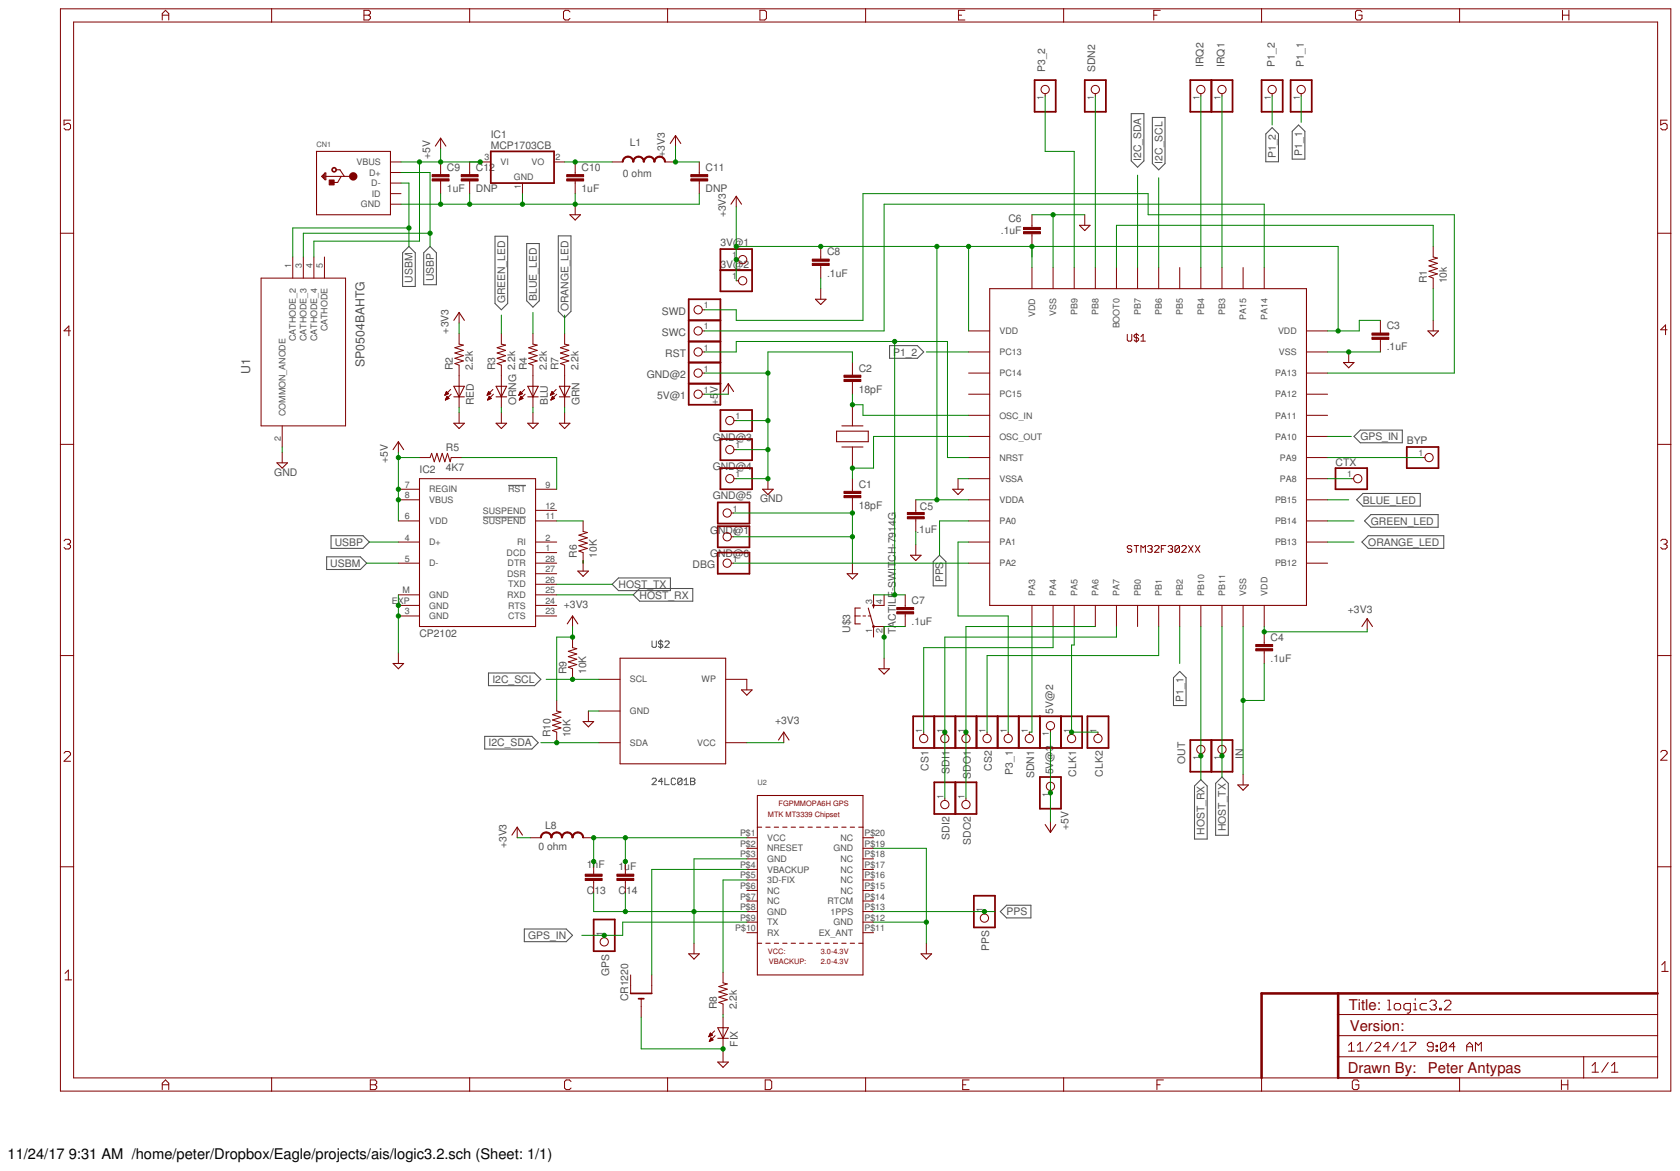
[picture p154: page 1]

11/24/17 9:31 AM /home/peter/Dropbox/Eagle/projects/ais/logic3.2.sch (Sheet: 1/1)
