peterantypas/maiana/eagle/logic.brd.pdf

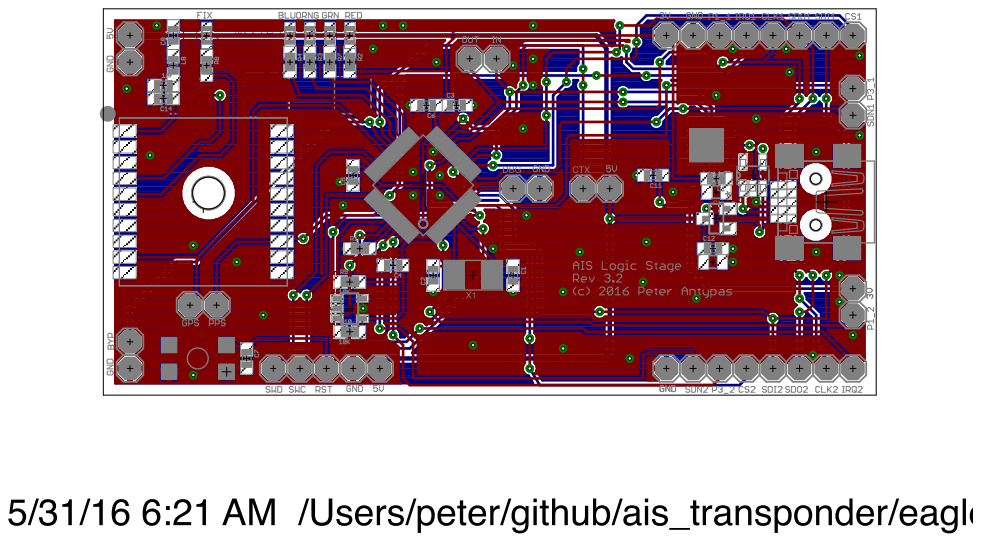
[picture p155: page 1]
