peterantypas/maiana/eagle/rf.brd.pdf

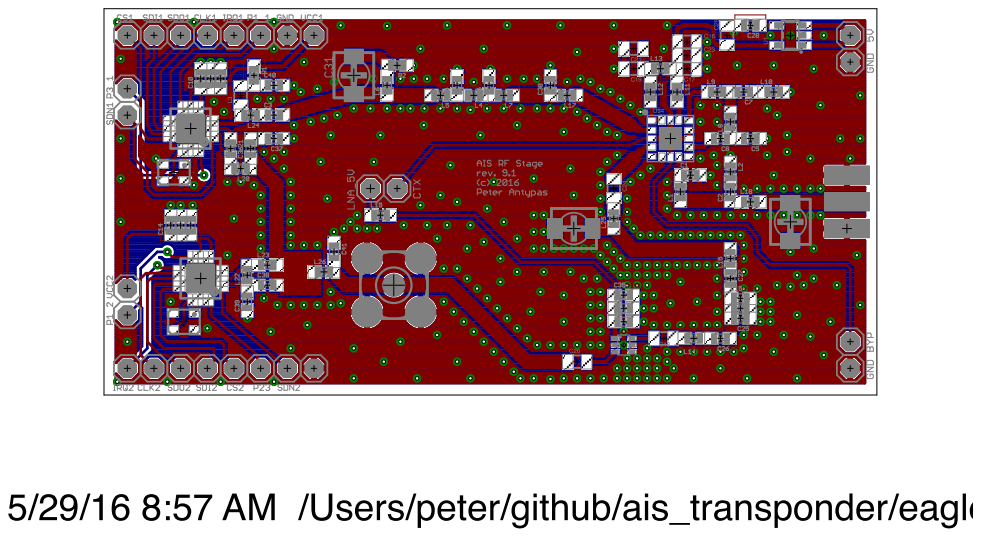
[picture p156: page 1]
