peterantypas/maiana/latest/CAD/NMEA0183Breakout/NMEA0183Breakout-3.0.brd

## EAGLE design latest/CAD/NMEA0183Breakout/NMEA0183Breakout-3.0.brd (2021-07-22)

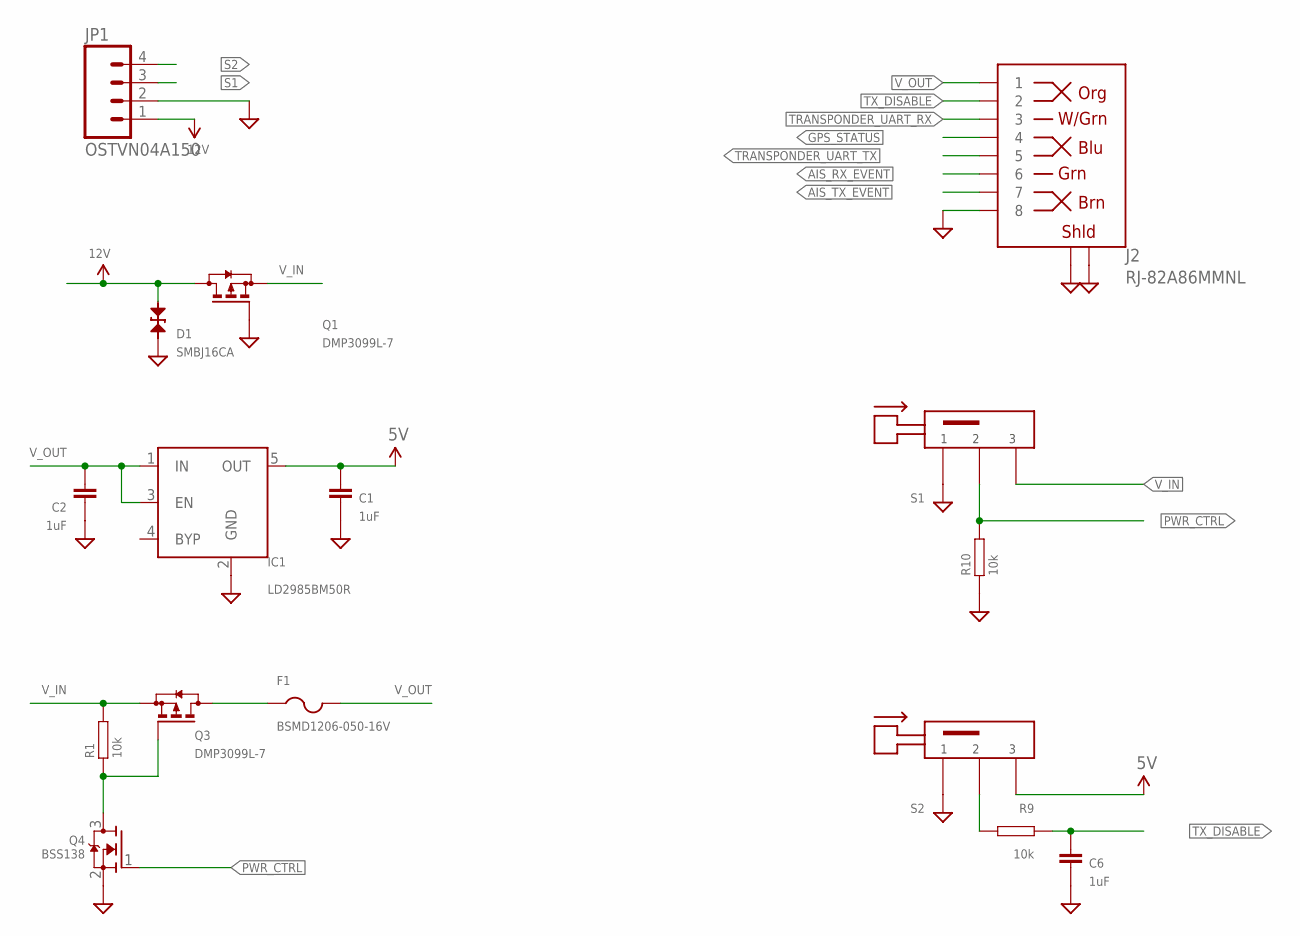
[picture p199: schematic NMEA0183Breakout-3.0.sch, sheet 1]

Parts:
C1, C2, C6: 1uF; 0603
D1: SMBJ16CA; SMB-BIDIR
F1: BSMD1206-050-16V; R1206
IC1: LD2985BM50R; SOT23-5
J2: RJ-82A86MMNL
JP1: OSTVN04A150; 1X04
Q1, Q3: DMP3099L-7; SOT23
Q4: BSS138; SOT23
R1, R9, R10: 10k; 0603
S1, S2: LC1258XXNP

Connections:
5V: C1.P$1 (1), IC1.5 (OUT), S2.P$3 (3); also elsewhere on the board
12V: D1.A, JP1.1, Q1.3 (D)
AIS_RX_EVENT: J2.P$6 (6); also elsewhere on the board
AIS_TX_EVENT: J2.P$7 (7); also elsewhere on the board
GND: C1.P$2 (2), C2.P$2 (2), C6.P$2 (2), D1.C, IC1.2 (GND), J2.P$8 (8), J2.P$9 (SHLD), J2.P$10 (SHLD), J2.P$11 (SHLD), J2.P$12 (SHLD), JP1.2, Q1.1 (G), Q4.2 (S), R10.P$1, S1.P$1 (1), S2.P$1 (1); also elsewhere on the board
GPS_STATUS: J2.P$4 (4); also elsewhere on the board
unnamed: R9.P$2, S2.P$2 (2)
unnamed: Q3.1 (G), Q4.3 (D), R1.P$1
unnamed: F1.1, Q3.3 (D)
PWR_CTRL: Q4.1 (G), R10.P$2, S1.P$2 (2)
S1: JP1.3; also elsewhere on the board
S2: JP1.4; also elsewhere on the board
TRANSPONDER_UART_RX: J2.P$3 (3); also elsewhere on the board
TRANSPONDER_UART_TX: J2.P$5 (5); also elsewhere on the board
TX_DISABLE: C6.P$1 (1), J2.P$2 (2), R9.P$1; also elsewhere on the board
V_IN: Q1.2 (S), Q3.2 (S), R1.P$2, S1.P$3 (3)
V_OUT: C2.P$1 (1), F1.2, IC1.1 (IN), IC1.3 (EN), J2.P$1 (1)

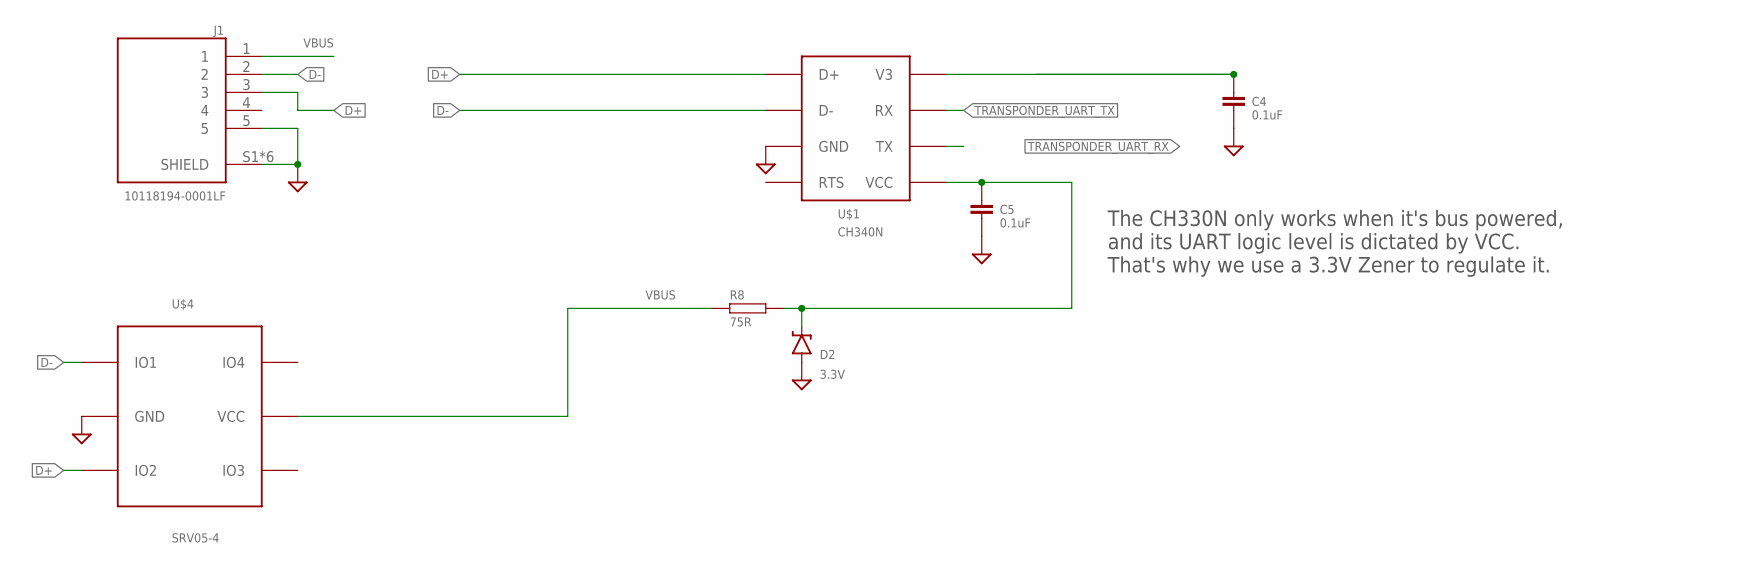
[picture p200: schematic NMEA0183Breakout-3.0.sch, sheet 2]

Parts:
C4, C5: 0.1uF; 0603
D2: 3.3V; SOD-323
J1: 10118194-0001LF; AMPHENOL_10118194-0001LF
R8: 75R; 0603
U$1: CH340N; SOIC-8; PARTNO CH340N
U$4: SRV05-4; SOT23-6

Connections:
D+: J1.3, U$1.1 (D+), U$4.3 (IO2)
D-: J1.2, U$1.2 (D-), U$4.1 (IO1)
GND: C4.P$2 (2), C5.P$2 (2), D2.A, J1.5, J1.S1 (SHIELD), J1.S2 (SHIELD), J1.S3 (SHIELD), J1.S4 (SHIELD), J1.S5 (SHIELD), J1.S6 (SHIELD), U$1.3 (GND), U$4.2 (GND); also elsewhere on the board
unnamed: C4.P$1 (1), U$1.8 (V3)
unnamed: C5.P$1 (1), D2.C, R8.P$2, U$1.5 (VCC)
TRANSPONDER_UART_RX: U$1.6 (TX); also elsewhere on the board
TRANSPONDER_UART_TX: U$1.7 (RX); also elsewhere on the board
VBUS: J1.1, R8.P$1, U$4.5 (VCC)

Notes on the sheet:
The CH330N only works when it's bus powered, and its UART logic level is dictated by VCC. That's why we use a 3.3V Zener to regulate it.

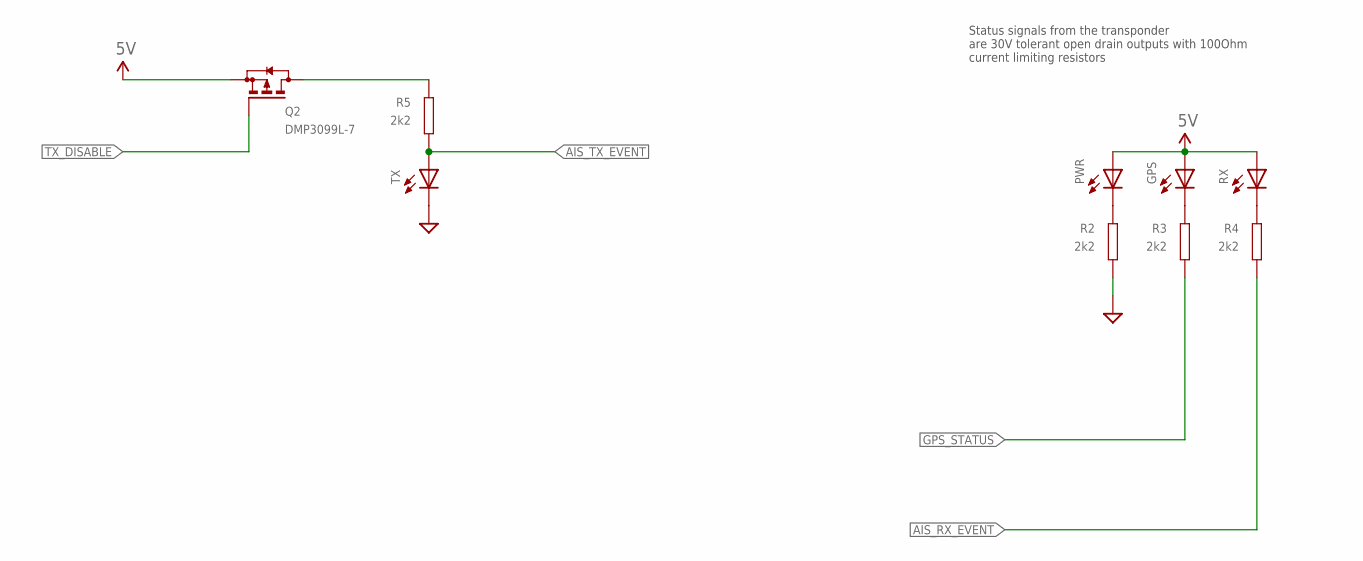
[picture p201: schematic NMEA0183Breakout-3.0.sch, sheet 3]

Parts:
GPS: LEDCHIPLED_1206; CHIPLED_1206; PARTNO TJ-S3216CL9T5ALC2G-A5
PWR: LEDCHIPLED_1206; CHIPLED_1206; PARTNO TJ-S3216CL9T5ALC2G-A5
Q2: DMP3099L-7; SOT23
R2, R3, R4, R5: 2k2; 0603
RX: LEDCHIPLED_1206; CHIPLED_1206; PARTNO TJ-S3216CL9T5ALC2G-A5
TX: LEDCHIPLED_1206; CHIPLED_1206; PARTNO TJ-S3216CL9T5ALC2G-A5

Connections:
5V: GPS.A, PWR.A, Q2.2 (S), RX.A; also elsewhere on the board
AIS_RX_EVENT: R4.P$2; also elsewhere on the board
AIS_TX_EVENT: R5.P$2, TX.A; also elsewhere on the board
GND: R2.P$2, TX.C; also elsewhere on the board
GPS_STATUS: R3.P$2; also elsewhere on the board
unnamed: PWR.C, R2.P$1
unnamed: GPS.C, R3.P$1
unnamed: R4.P$1, RX.C
unnamed: Q2.3 (D), R5.P$1
TX_DISABLE: Q2.1 (G); also elsewhere on the board

Notes on the sheet:
Status signals from the transponder are 30V tolerant open drain outputs with 100Ohm current limiting resistors

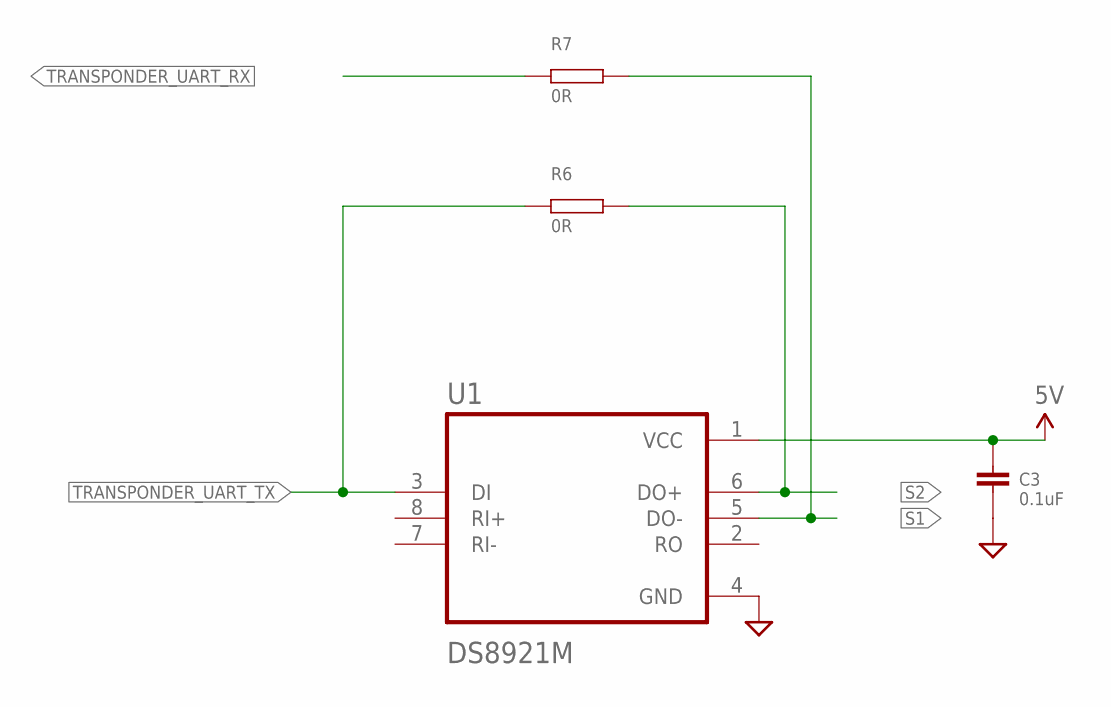
[picture p202: schematic NMEA0183Breakout-3.0.sch, sheet 4]

Parts:
C3: 0.1uF; 0603
R6, R7: 0R; 0603
U1: DS8921M; SOIC127P599X175-8N

Connections:
5V: C3.P$1 (1), U1.1 (VCC); also elsewhere on the board
GND: C3.P$2 (2), U1.4 (GND); also elsewhere on the board
S1: R7.P$2, U1.5 (DO-); also elsewhere on the board
S2: R6.P$2, U1.6 (DO+); also elsewhere on the board
TRANSPONDER_UART_RX: R7.P$1; also elsewhere on the board
TRANSPONDER_UART_TX: R6.P$1, U1.3 (DI); also elsewhere on the board

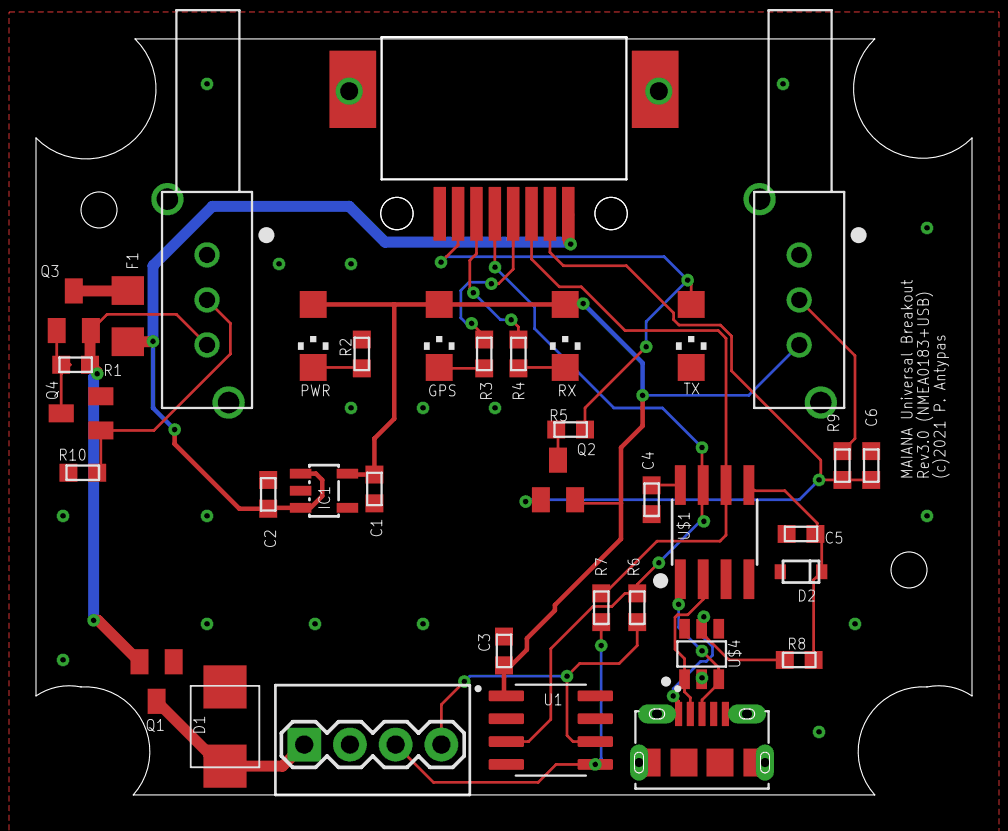
[picture p203: board NMEA0183Breakout-3.0.brd from above]

Board: 2 copper layers, 52.0 x 42.0 mm, 36 parts (0 on the bottom side), 26 nets.
