peterantypas/maiana/latest/CAD/USBBreakout/USBBreakout-2.0.brd

## EAGLE design latest/CAD/USBBreakout/USBBreakout-2.0.brd (2021-07-22)

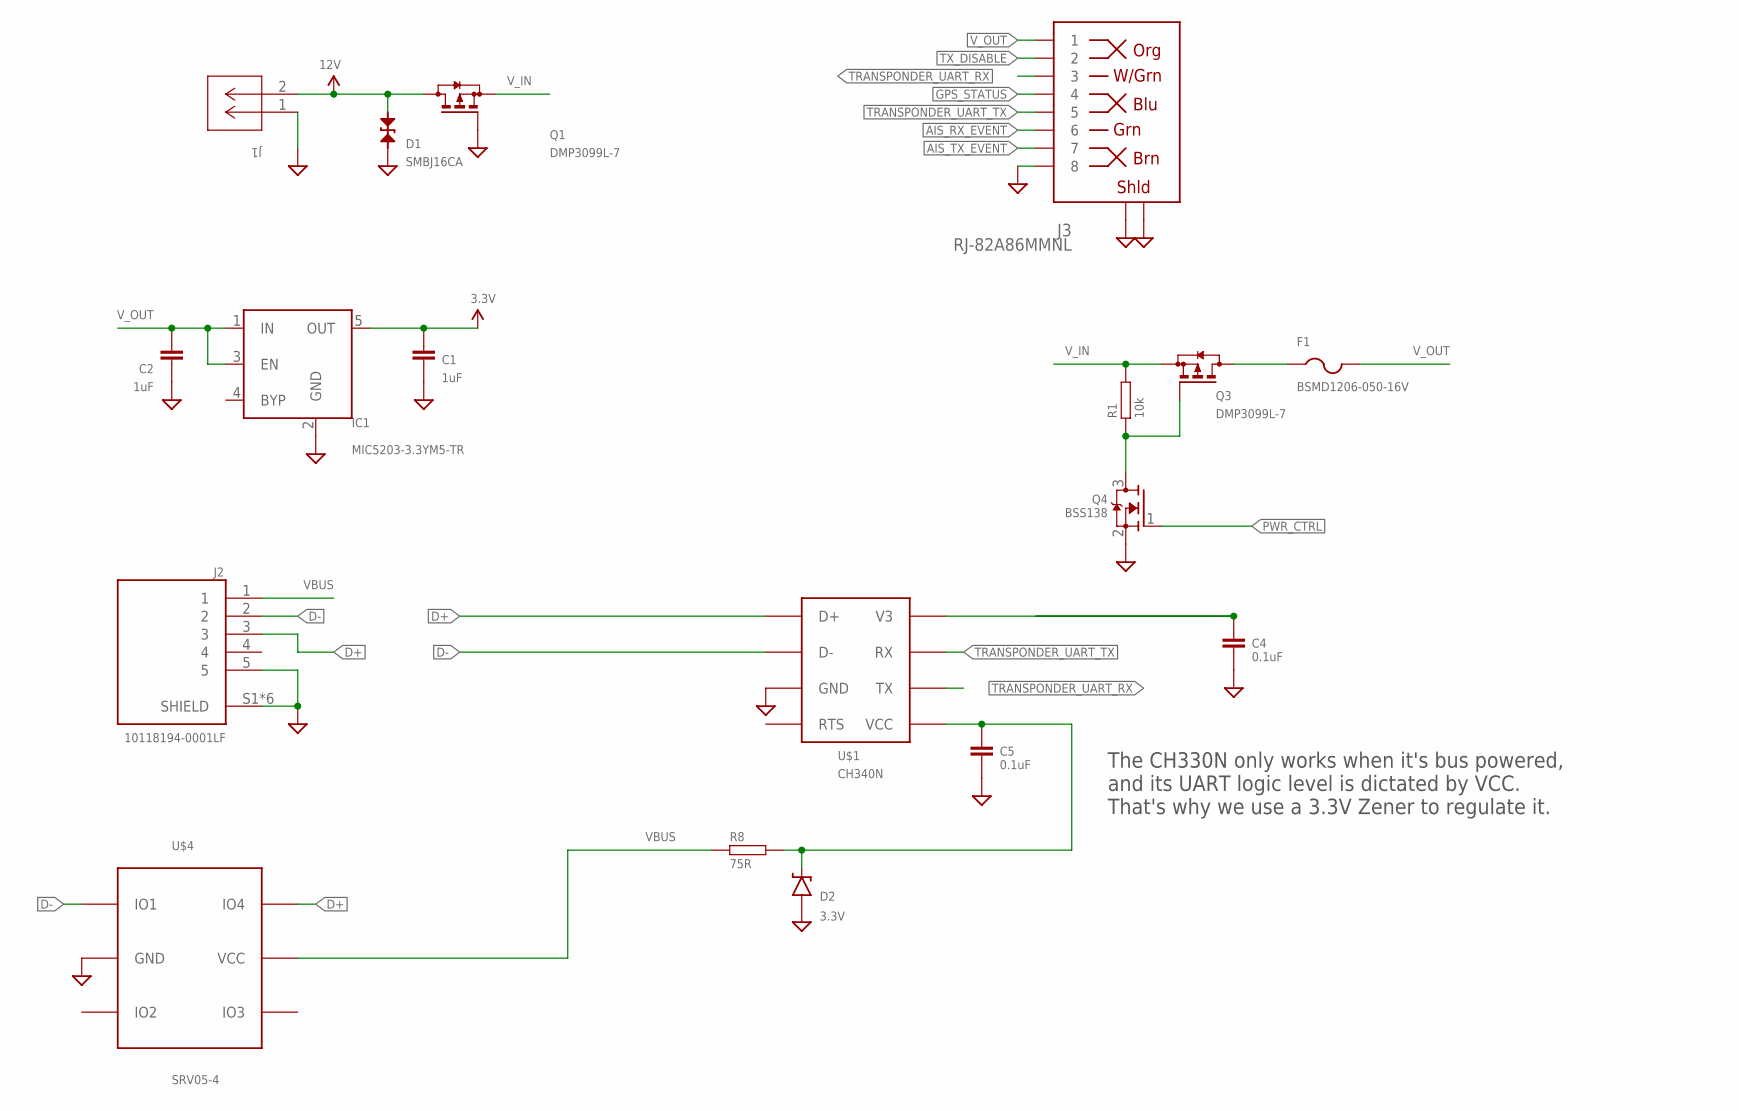
[picture p204: schematic USBBreakout-2.0.sch, sheet 1]

Parts:
C1, C2: 1uF; 0603
C4, C5: 0.1uF; 0603
D1: SMBJ16CA; SMB-BIDIR
D2: 3.3V; SOD-323
F1: BSMD1206-050-16V; R1206
IC1: MIC5203-3.3YM5-TR; SOT23-5
J1: OSTVN02A150; CONN_OSTVN02A150_OST
J2: 10118194-0001LF; AMPHENOL_10118194-0001LF
J3: RJ-82A86MMNL
Q1, Q3: DMP3099L-7; SOT23
Q4: BSS138; SOT23
R1: 10k; 0603
R8: 75R; 0603
U$1: CH340N; SOIC-8; PARTNO CH340N
U$4: SRV05-4; SOT23-6

Connections:
3.3V: C1.P$1 (1), IC1.5 (OUT); also elsewhere on the board
12V: D1.A, J1.2, Q1.3 (D)
AIS_RX_EVENT: J3.P$6 (6); also elsewhere on the board
AIS_TX_EVENT: J3.P$7 (7); also elsewhere on the board
D+: J2.3, U$1.1 (D+), U$4.6 (IO4)
D-: J2.2, U$1.2 (D-), U$4.1 (IO1)
GND: C1.P$2 (2), C2.P$2 (2), C4.P$2 (2), C5.P$2 (2), D1.C, D2.A, IC1.2 (GND), J1.1, J2.5, J2.S1 (SHIELD), J2.S2 (SHIELD), J2.S3 (SHIELD), J2.S4 (SHIELD), J2.S5 (SHIELD), J2.S6 (SHIELD), J3.P$8 (8), J3.P$9 (SHLD), J3.P$10 (SHLD), J3.P$11 (SHLD), J3.P$12 (SHLD), Q1.1 (G), Q4.2 (S), U$1.3 (GND), U$4.2 (GND); also elsewhere on the board
GPS_STATUS: J3.P$4 (4); also elsewhere on the board
unnamed: C4.P$1 (1), U$1.8 (V3)
unnamed: Q3.1 (G), Q4.3 (D), R1.P$1
unnamed: F1.1, Q3.3 (D)
unnamed: C5.P$1 (1), D2.C, R8.P$2, U$1.5 (VCC)
PWR_CTRL: Q4.1 (G); also elsewhere on the board
TRANSPONDER_UART_RX: J3.P$3 (3), U$1.6 (TX)
TRANSPONDER_UART_TX: J3.P$5 (5), U$1.7 (RX)
TX_DISABLE: J3.P$2 (2); also elsewhere on the board
VBUS: J2.1, R8.P$1, U$4.5 (VCC)
V_IN: Q1.2 (S), Q3.2 (S), R1.P$2; also elsewhere on the board
V_OUT: C2.P$1 (1), F1.2, IC1.1 (IN), IC1.3 (EN), J3.P$1 (1)

Notes on the sheet:
The CH330N only works when it's bus powered, and its UART logic level is dictated by VCC. That's why we use a 3.3V Zener to regulate it.

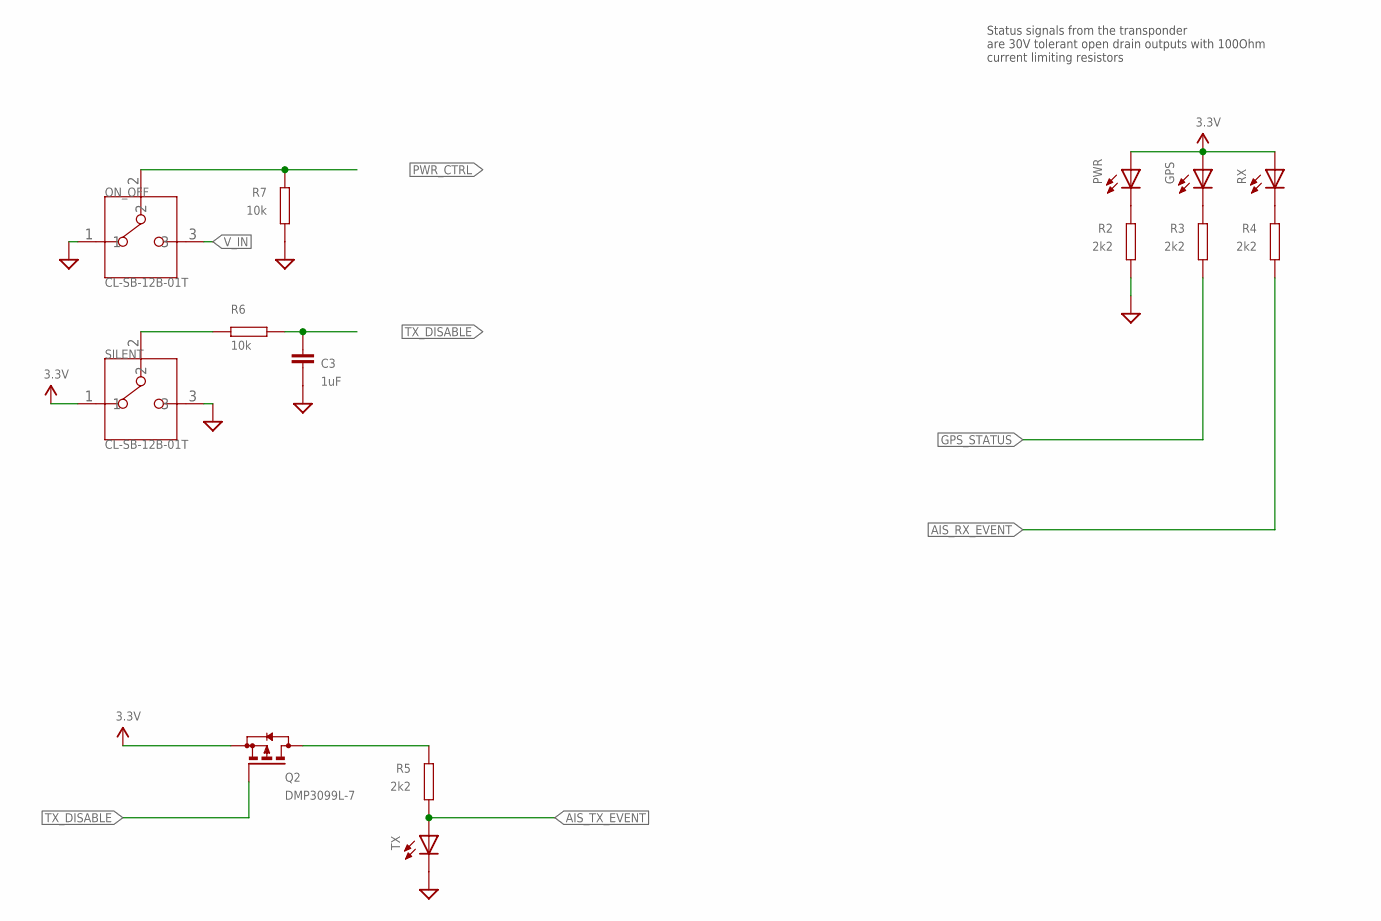
[picture p205: schematic USBBreakout-2.0.sch, sheet 2]

Parts:
C3: 1uF; 0603
GPS: LEDCHIPLED_1206; CHIPLED_1206; PARTNO TJ-S3216CL9T5ALC2G-A5
ON_OFF: CL-SB-12B-01T; CL-SB-12B
PWR: LEDCHIPLED_1206; CHIPLED_1206; PARTNO TJ-S3216CL9T5ALC2G-A5
Q2: DMP3099L-7; SOT23
R2, R3, R4, R5: 2k2; 0603
R6, R7: 10k; 0603
RX: LEDCHIPLED_1206; CHIPLED_1206; PARTNO TJ-S3216CL9T5ALC2G-A5
SILENT: CL-SB-12B-01T; CL-SB-12B
TX: LEDCHIPLED_1206; CHIPLED_1206; PARTNO TJ-S3216CL9T5ALC2G-A5

Connections:
3.3V: GPS.A, PWR.A, Q2.2 (S), RX.A, SILENT.1; also elsewhere on the board
AIS_RX_EVENT: R4.P$2; also elsewhere on the board
AIS_TX_EVENT: R5.P$2, TX.A; also elsewhere on the board
GND: C3.P$2 (2), ON_OFF.1, R2.P$2, R7.P$2, SILENT.3, TX.C; also elsewhere on the board
GPS_STATUS: R3.P$2; also elsewhere on the board
unnamed: PWR.C, R2.P$1
unnamed: GPS.C, R3.P$1
unnamed: R4.P$1, RX.C
unnamed: R6.P$1, SILENT.2
unnamed: Q2.3 (D), R5.P$1
PWR_CTRL: ON_OFF.2, R7.P$1; also elsewhere on the board
TX_DISABLE: C3.P$1 (1), Q2.1 (G), R6.P$2; also elsewhere on the board
V_IN: ON_OFF.3; also elsewhere on the board

Notes on the sheet:
Status signals from the transponder are 30V tolerant open drain outputs with 100Ohm current limiting resistors

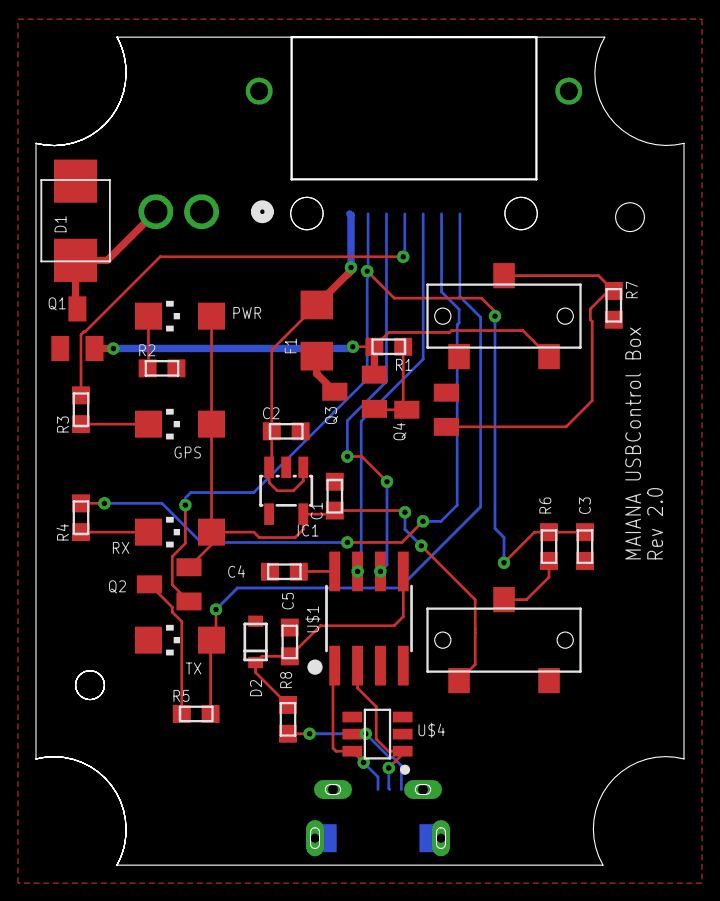
[picture p206: board USBBreakout-2.0.brd from above]

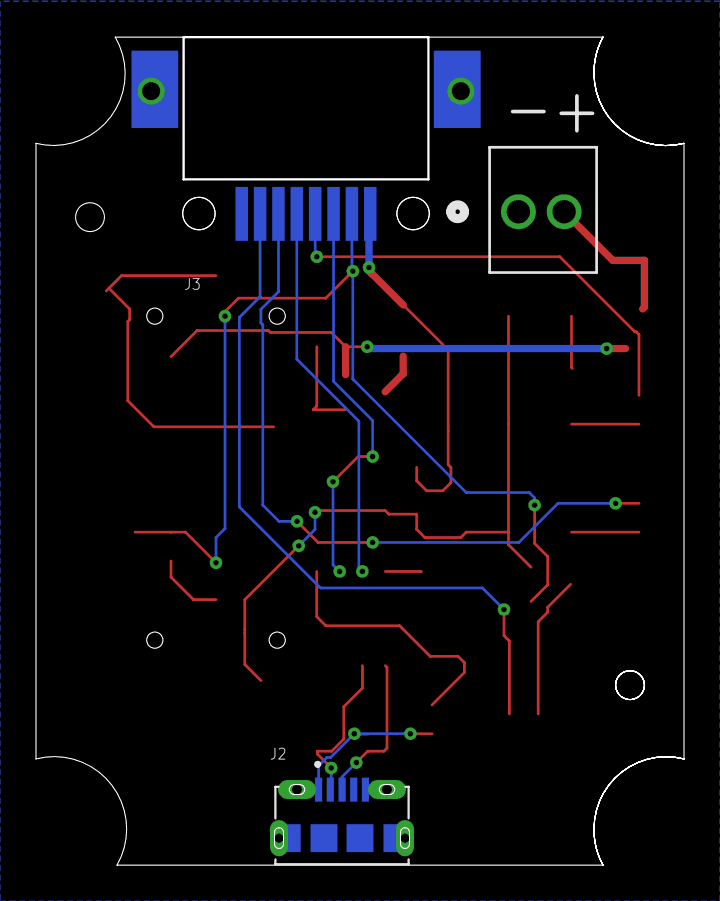
[picture p207: board USBBreakout-2.0.brd from below]

Board: 2 copper layers, 36.0 x 46.0 mm, 32 parts (3 on the bottom side), 24 nets.
