peterantypas/maiana/latest/CAD/Board-10.5/rj45-breakout-10.5.0.brd

## EAGLE design latest/CAD/Board-10.5/rj45-breakout-10.5.0.brd (2021-06-01)

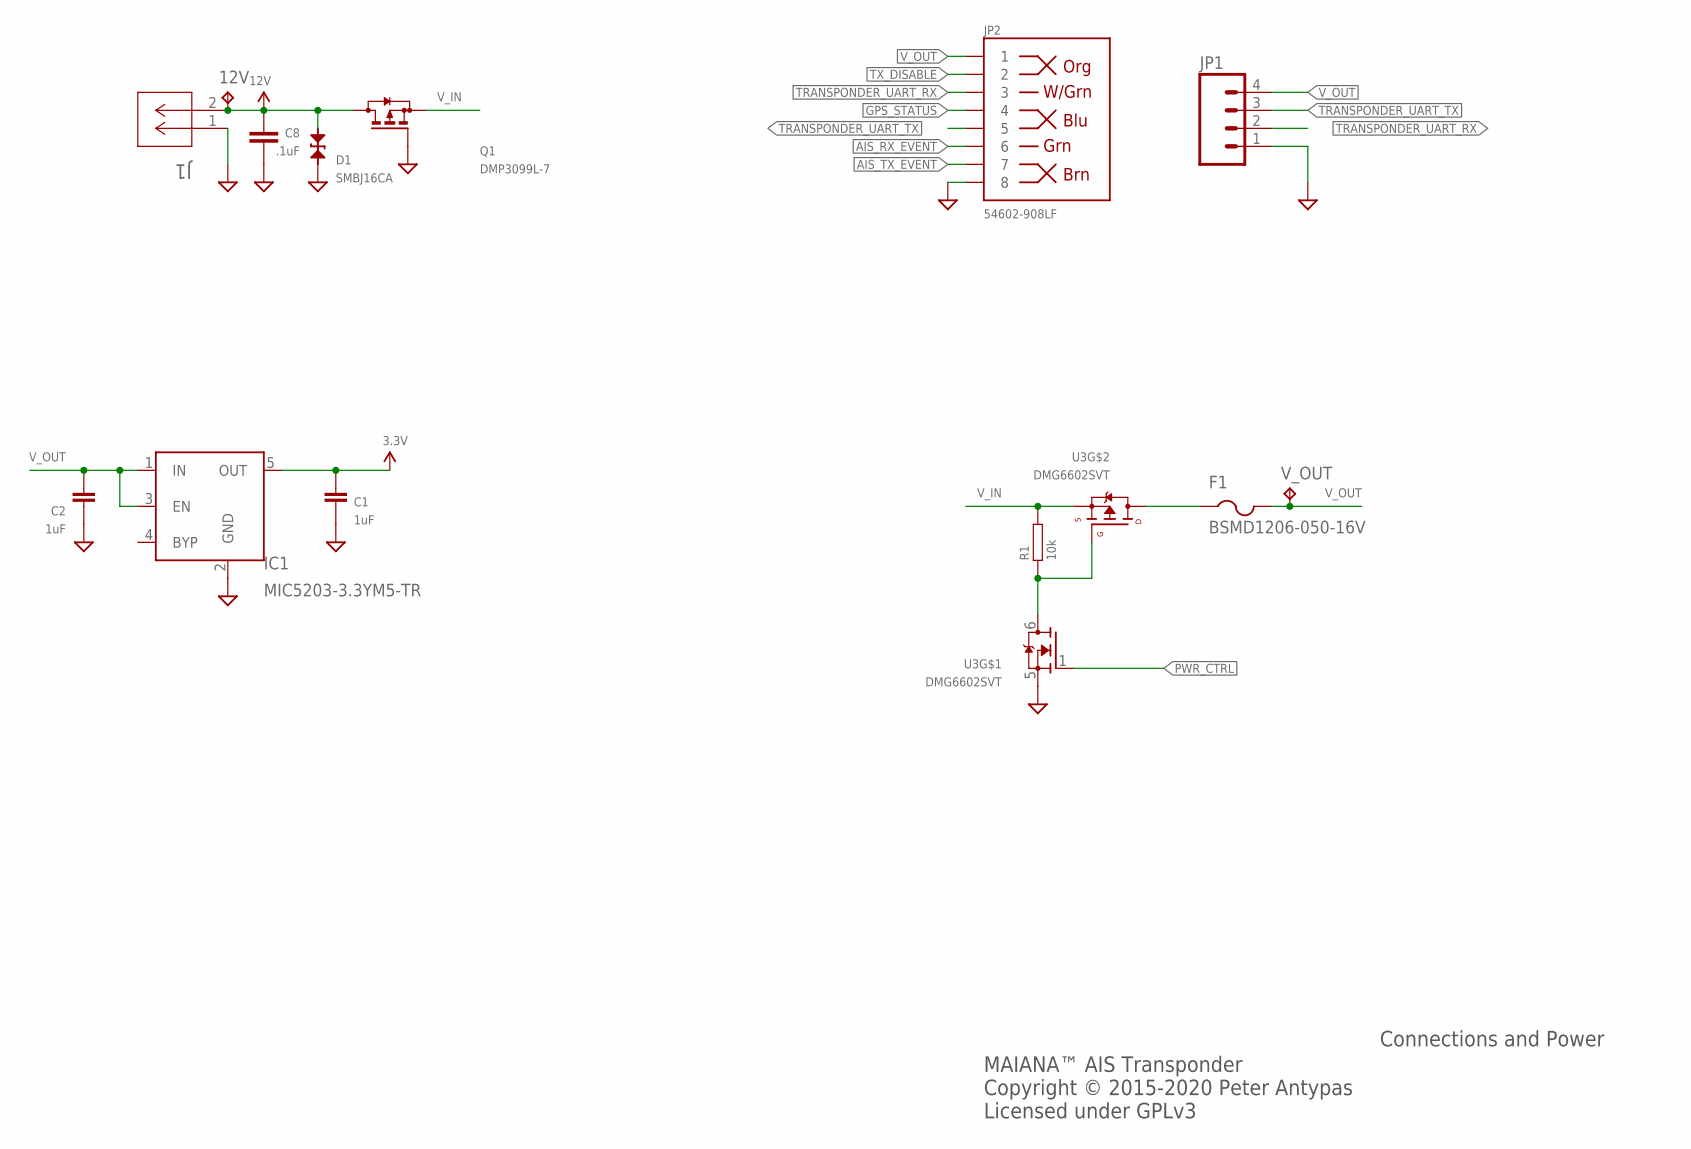
[picture p208: schematic rj45-breakout-10.5.0.sch, sheet 1]

Parts:
12V: TPTP20R; TP20R
C1, C2: 1uF; 0603
C8: .1uF; 0603-CAP; PARTNO GRM188R71E223KA01D
D1: SMBJ16CA; SMB-BIDIR
F1: BSMD1206-050-16V; R1206
IC1: MIC5203-3.3YM5-TR; SOT23-5
J1: OSTVN02A150; CONN_OSTVN02A150_OST
JP1: M04PTH; 1X04
JP2: 54602-908LF; RJ45-8
Q1: DMP3099L-7; SOT23
R1: 10k; 0603
U3: DMG6602SVT; SOT23-6
V_OUT: TPTP20R; TP20R

Connections:
3.3V: C1.P$1 (1), IC1.5 (OUT); also elsewhere on the board
12V: 12V.TP, C8.1, D1.A, J1.2, Q1.3 (D)
AIS_RX_EVENT: JP2.6; also elsewhere on the board
AIS_TX_EVENT: JP2.7; also elsewhere on the board
GND: C1.P$2 (2), C2.P$2 (2), C8.2, D1.C, IC1.2 (GND), J1.1, JP1.1, JP2.8, Q1.1 (G), U3.5 (S); also elsewhere on the board
GPS_STATUS: JP2.4; also elsewhere on the board
unnamed: R1.P$1, U3.3 (G), U3.6 (D)
unnamed: F1.1, U3.4 (D)
PWR_CTRL: U3.1 (G); also elsewhere on the board
TRANSPONDER_UART_RX: JP1.2, JP2.3
TRANSPONDER_UART_TX: JP1.3, JP2.5
TX_DISABLE: JP2.2; also elsewhere on the board
V_IN: Q1.2 (S), R1.P$2, U3.2 (S); also elsewhere on the board
V_OUT: C2.P$1 (1), F1.2, IC1.1 (IN), IC1.3 (EN), JP1.4, JP2.1, V_OUT.TP

Notes on the sheet:
MAIANA™ AIS Transponder Copyright © 2015-2020 Peter Antypas Licensed under GPLv3
Connections and Power
