peterantypas/maiana/latest/CAD/Board-10.5/rj45-breakout-10.5.0.brd

## EAGLE design latest/CAD/Board-10.5/rj45-breakout-10.5.0.brd (continued)

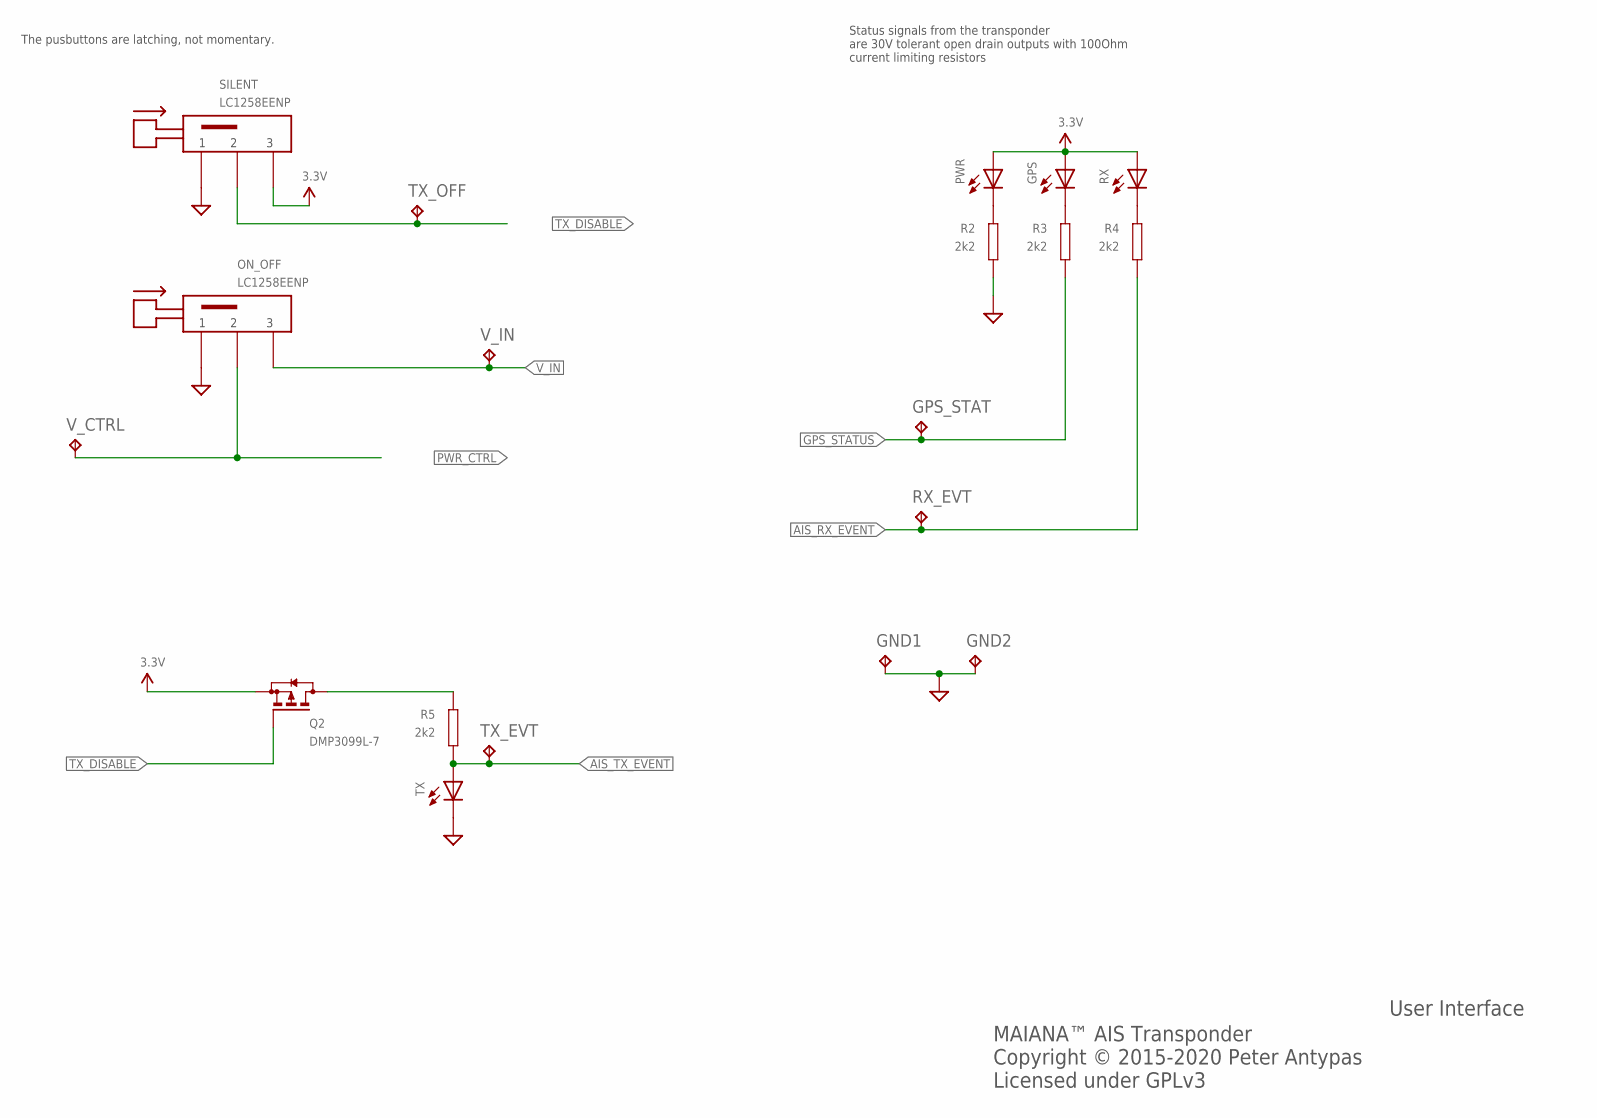
[picture p209: schematic rj45-breakout-10.5.0.sch, sheet 2]

Parts:
GND1, GND2: TPTP20R; TP20R
GPS: LEDCHIPLED_1206; CHIPLED_1206
GPS_STAT: TPTP20R; TP20R
ON_OFF: LC1258EENP; LC1258XXNP
PWR: LEDCHIPLED_1206; CHIPLED_1206
Q2: DMP3099L-7; SOT23
R2, R3, R4, R5: 2k2; 0603
RX: LEDCHIPLED_1206; CHIPLED_1206
RX_EVT: TPTP20R; TP20R
SILENT: LC1258EENP; LC1258XXNP
TX: LEDCHIPLED_1206; CHIPLED_1206
TX_EVT: TPTP20R; TP20R
TX_OFF: TPTP20R; TP20R
V_CTRL: TPTP20R; TP20R
V_IN: TPTP20R; TP20R

Connections:
3.3V: GPS.A, PWR.A, Q2.2 (S), RX.A, SILENT.P$3 (3); also elsewhere on the board
AIS_RX_EVENT: R4.P$2, RX_EVT.TP; also elsewhere on the board
AIS_TX_EVENT: R5.P$2, TX.A, TX_EVT.TP; also elsewhere on the board
GND: GND1.TP, GND2.TP, ON_OFF.P$1 (1), R2.P$2, SILENT.P$1 (1), TX.C; also elsewhere on the board
GPS_STATUS: GPS_STAT.TP, R3.P$2; also elsewhere on the board
unnamed: PWR.C, R2.P$1
unnamed: GPS.C, R3.P$1
unnamed: R4.P$1, RX.C
unnamed: Q2.3 (D), R5.P$1
PWR_CTRL: ON_OFF.P$2 (2), V_CTRL.TP; also elsewhere on the board
TX_DISABLE: Q2.1 (G), SILENT.P$2 (2), TX_OFF.TP; also elsewhere on the board
V_IN: ON_OFF.P$3 (3), V_IN.TP; also elsewhere on the board

Notes on the sheet:
MAIANA™ AIS Transponder Copyright © 2015-2020 Peter Antypas Licensed under GPLv3
User Interface
The pusbuttons are latching, not momentary.
Status signals from the transponder are 30V tolerant open drain outputs with 100Ohm current limiting resistors

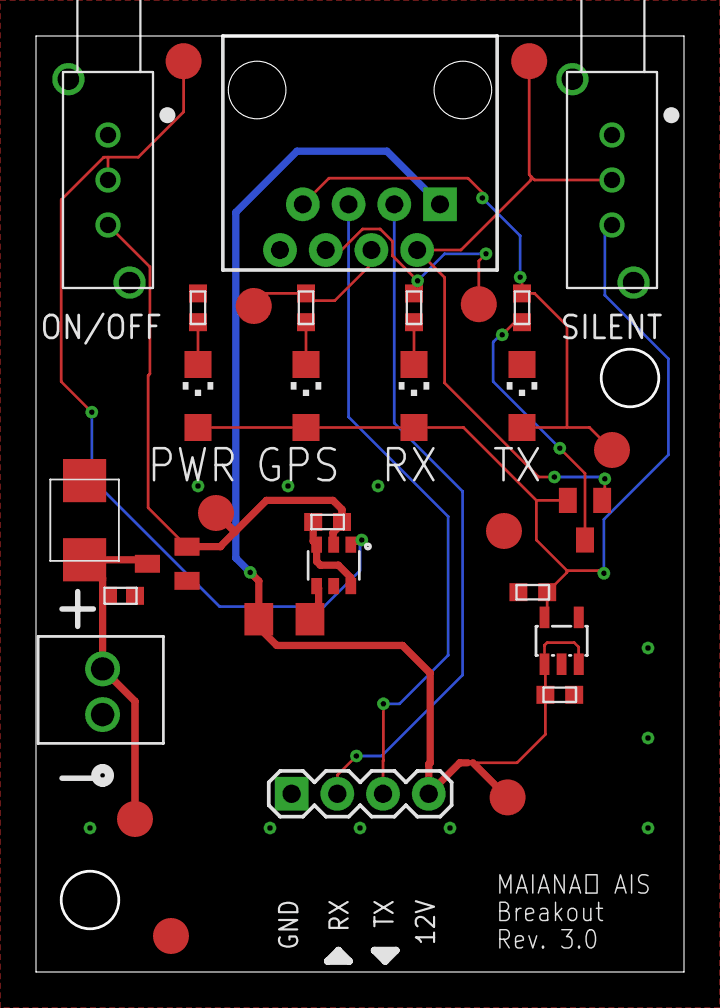
[picture p210: board rj45-breakout-10.5.0.brd from above]

Board: 2 copper layers, 36.0 x 52.0 mm, 33 parts (0 on the bottom side), 18 nets.
