peterantypas/maiana/latest/CAD/Board-10.0/rj45-breakout-10.0.brd

## EAGLE design latest/CAD/Board-10.0/rj45-breakout-10.0.brd (2020-12-13)

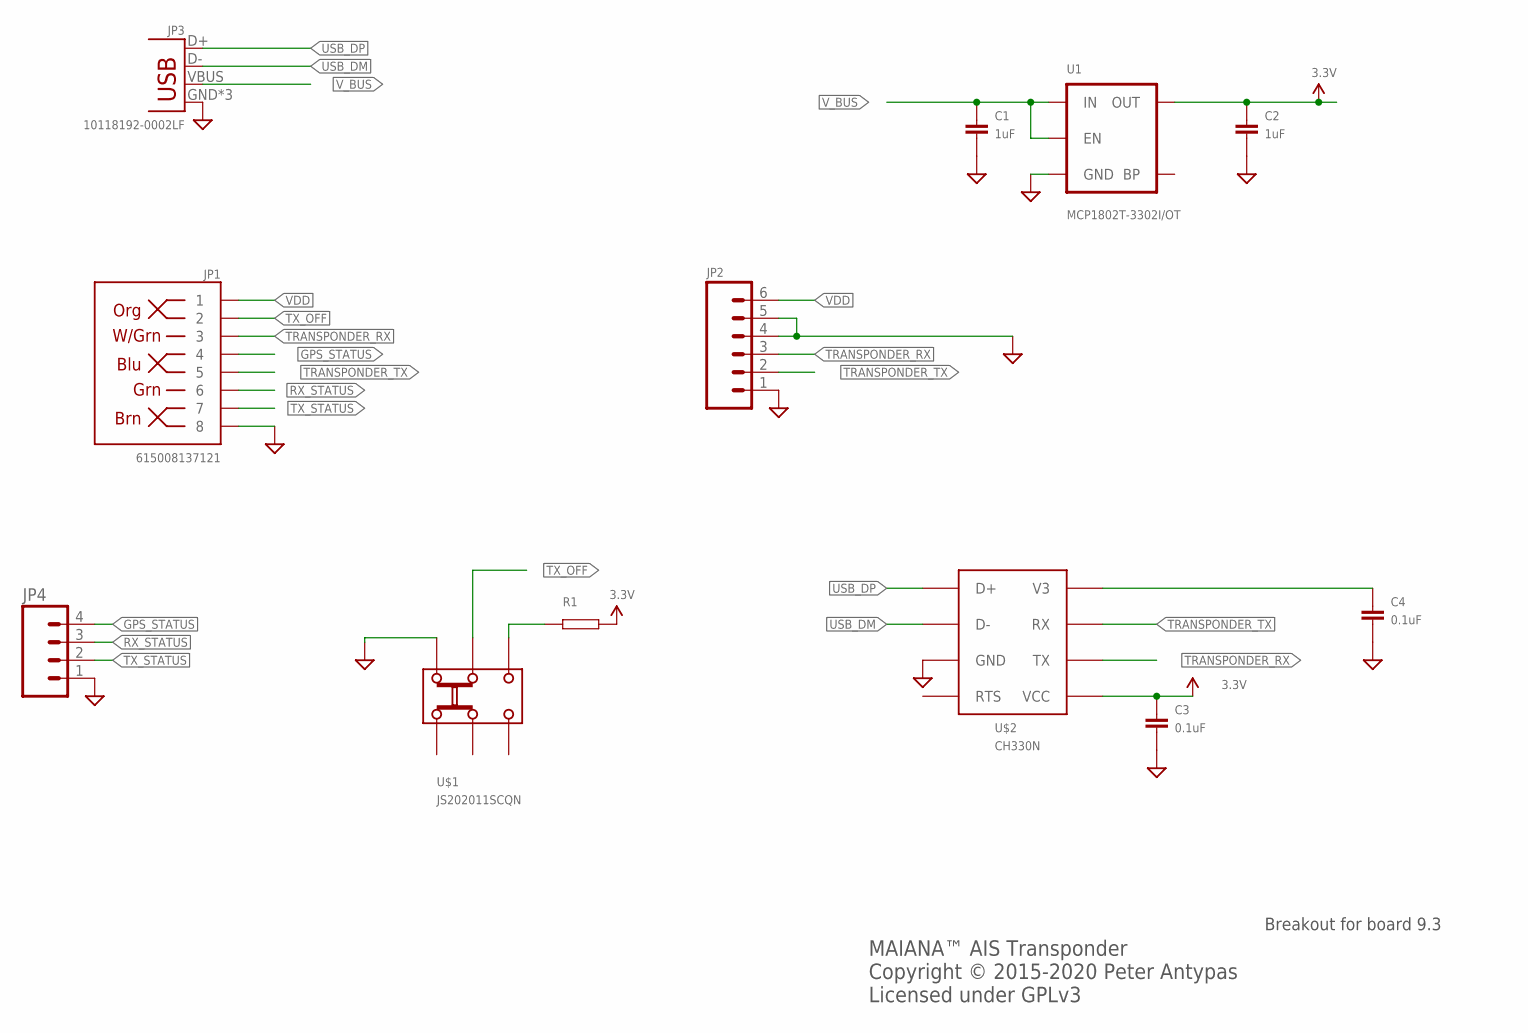
[picture p211: schematic rj45-breakout-10.0.sch]

Parts:
C1, C2: 1uF; 0603
C3, C4: 0.1uF; 0603
JP1: 615008137121; RJ45-8
JP2: M06SILK_FEMALE_PTH; 1X06
JP3: 10118192-0002LF; USB-MICROB
JP4: M04PTH; 1X04
R1: RESISTOR0603; 0603
U1: MCP1802T-3302I/OT; SOT23-5
U$1: JS202011SCQN; DPDT-SMD
U$2: CH330N; SOIC-8

Connections:
3.3V: C2.P$1 (1), C3.P$1 (1), R1.P$2, U1.5 (OUT), U$2.5 (VCC)
GND: C1.P$2 (2), C2.P$2 (2), C3.P$2 (2), C4.P$2 (2), JP1.8, JP2.1, JP2.4, JP2.5, JP3.GND, JP3.MT1 (GND), JP3.MT2 (GND), JP4.1, U1.2 (GND), U$1.P$6, U$2.3 (GND)
GPS_STATUS: JP1.4, JP4.4
unnamed: C4.P$1 (1), U$2.8 (V3)
unnamed: R1.P$1, U$1.P$4
RX_STATUS: JP1.6, JP4.3
TRANSPONDER_RX: JP1.3, JP2.3, U$2.6 (TX)
TRANSPONDER_TX: JP1.5, JP2.2, U$2.7 (RX)
TX_OFF: JP1.2, U$1.P$5
TX_STATUS: JP1.7, JP4.2
USB_DM: JP3.D-, U$2.2 (D-)
USB_DP: JP3.D+, U$2.1 (D+)
VDD: JP1.1, JP2.6
V_BUS: C1.P$1 (1), JP3.VBUS, U1.1 (IN), U1.3 (EN)

Notes on the sheet:
MAIANA™ AIS Transponder Copyright © 2015-2020 Peter Antypas Licensed under GPLv3
Breakout for board 9.3

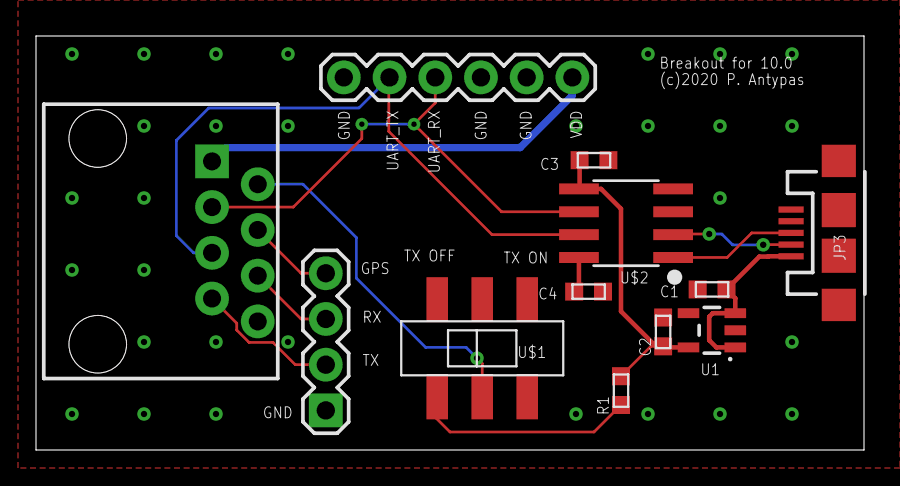
[picture p212: board rj45-breakout-10.0.brd from above]

Board: 2 copper layers, 46.0 x 23.0 mm, 12 parts (0 on the bottom side), 14 nets.
