peterantypas/maiana/eagle/logic.brd

## EAGLE design legacy/eagle/logic.brd (2017-11-24, an earlier design)

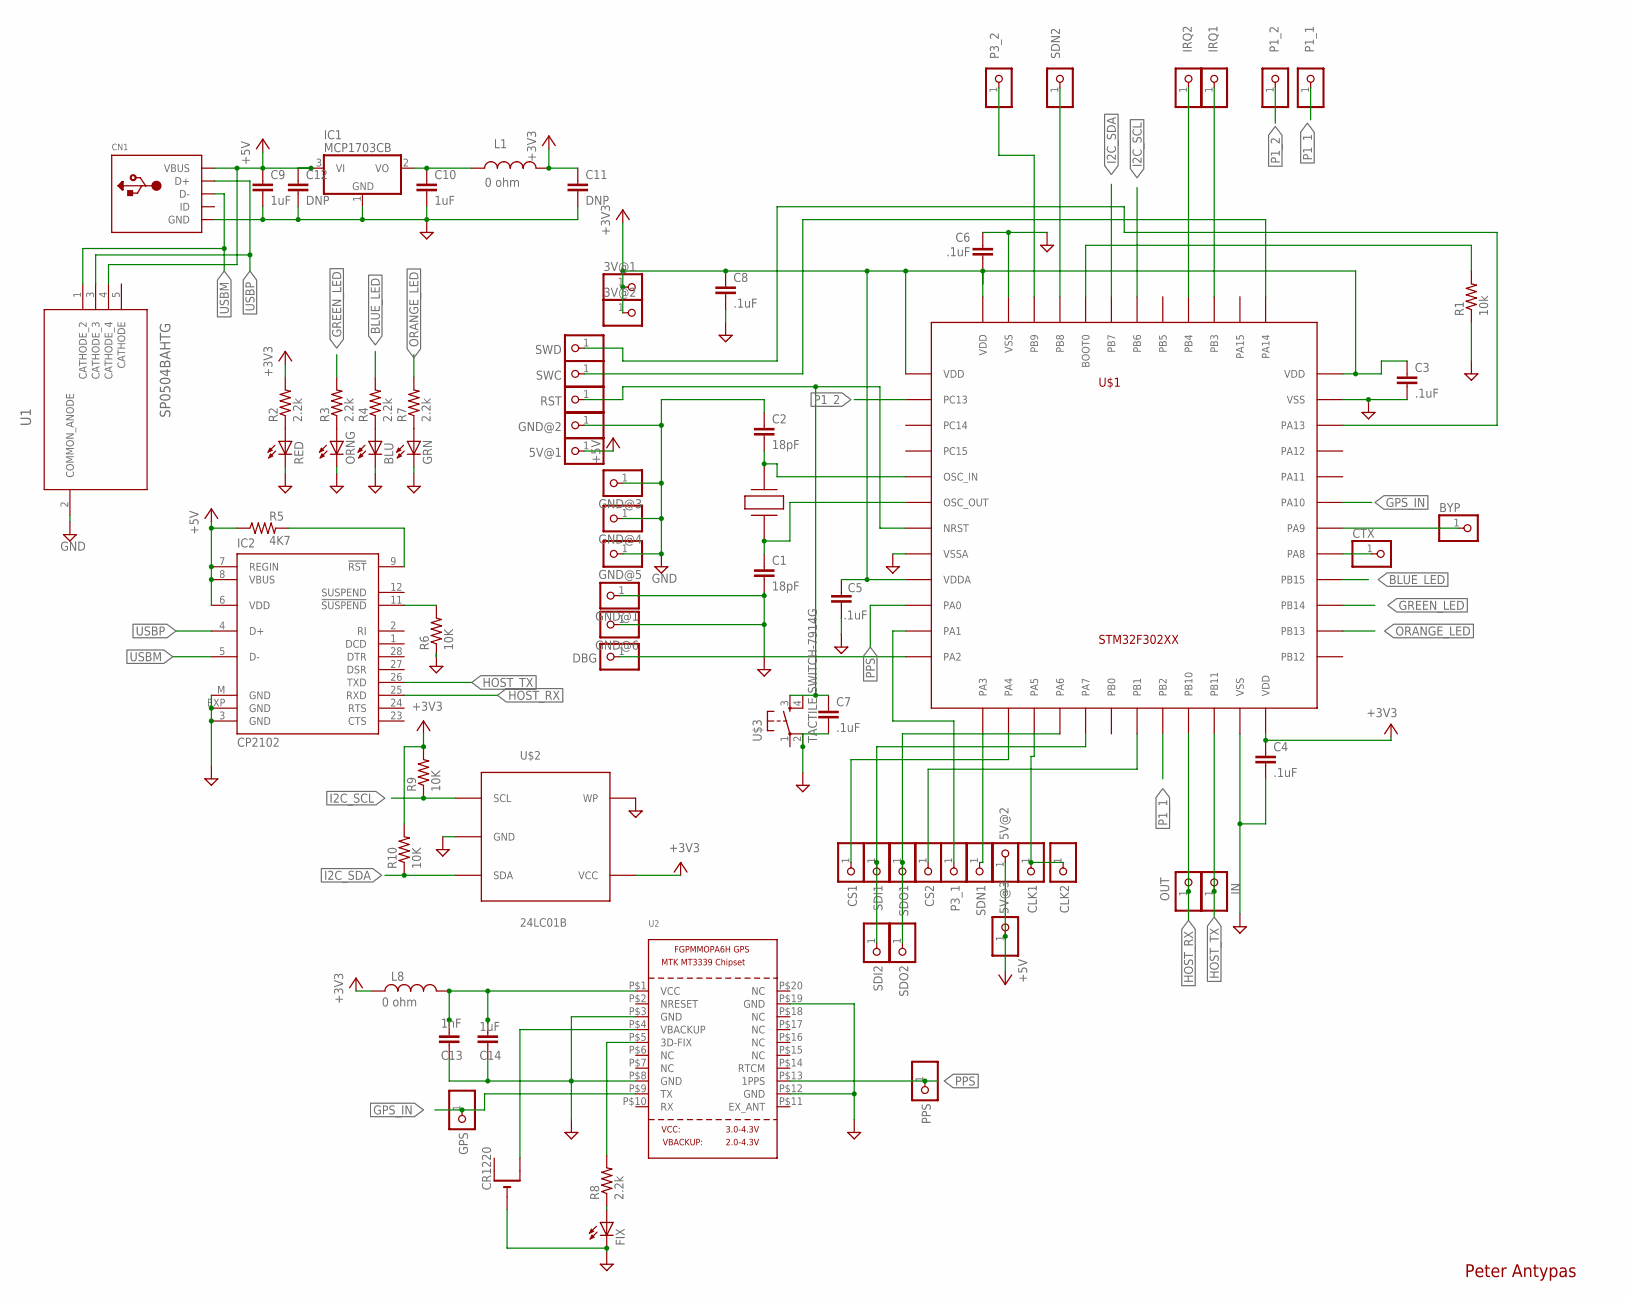
[picture p213: schematic logic.sch]

Parts:
3V@1, 3V@2, 5V@1, 5V@2, 5V@3: PINHD-1X1; 1X01
BLU: LEDCHIP-LED0603; CHIP-LED0603
BYP: PINHD-1X1; 1X01
C1, C2: 18pF; 0603-CAP
C3, C4, C5, C6, C7, C8: .1uF; 0603-CAP
C9, C10: 1uF; 0805
C11, C12: DNP; 0603-CAP
C13: 1nF; 0603-CAP
C14: 1uF; 0603-CAP
CLK1, CLK2: PINHD-1X1; 1X01
CN1: USBMINIB; USB-MINIB
CR1220: CR1220SMT; CR1220-SMD
CS1, CS2: PINHD-1X1; 1X01
CTX: PINHD-1X1; 1X01
DBG: PINHD-1X1; 1X01
FIX: LEDCHIP-LED0603; CHIP-LED0603
GND@1, GND@2, GND@3, GND@4, GND@5, GND@6: PINHD-1X1; 1X01
GPS: PINHD-1X1; 1X01
GRN: LEDCHIP-LED0603; CHIP-LED0603
IC1: MCP1703CB; SOT23
IC2: CP2102; MLP28
IN: PINHD-1X1; 1X01
IRQ1, IRQ2: PINHD-1X1; 1X01
L1, L8: 0 ohm; 0603
ORNG: LEDCHIP-LED0603; CHIP-LED0603
OUT: PINHD-1X1; 1X01
P1_1, P1_2, P3_1, P3_2: PINHD-1X1; 1X01
PPS: PINHD-1X1; 1X01
R1: 10k; 0603-RES
R2, R3, R4, R7, R8: 2.2k; 0603-RES
R5: 4K7; 0603-RES
R6, R9, R10: 10K; 0603-RES
RED: LEDCHIP-LED0603; CHIP-LED0603
RST: PINHD-1X1; 1X01
SDI1, SDI2: PINHD-1X1; 1X01
SDN1, SDN2: PINHD-1X1; 1X01
SDO1, SDO2: PINHD-1X1; 1X01
SWC: PINHD-1X1; 1X01
SWD: PINHD-1X1; 1X01
U1: SP0504BAHTG; SOT95P280X145-5N
U2: GPS_FGPMMOPA6H; FGPMMOPA6H
U$1: STM32F302XX; LQFP48
U$2: 24LC01B; SOT23-5
U$3: TACTILE-SWITCH-7914G; 7914G
X1: TXC_7A

Connections:
+3V3: 3V@1.1, 3V@2.1, C3.1, C4.1, C5.2, C6.1, C8.1, C11.1, L1.2, L8.1, R2.2, R9.2, R10.2, U$1.P$1 (VDD), U$1.P$9 (VDDA), U$1.P$24 (VDD), U$1.P$36 (VDD), U$1.P$48 (VDD), U$2.4 (VCC)
+5V: 5V@1.1, 5V@2.1, 5V@3.1, C9.1, C12.1, CN1.VBUS, IC1.3 (VI), IC2.6 (VDD), IC2.7 (REGIN), IC2.8 (VBUS), R5.1, U1.4 (CATHODE_4)
BLUE_LED: R4.2, U$1.P$28 (PB15)
EEPROM_CS: C7.1, RST.1, U$1.P$7 (NRST), U$3.3
GND: BLU.C, C1.2, C2.1, C3.2, C4.2, C5.1, C6.2, C7.2, C8.2, C9.2, C10.2, C11.2, C12.2, C13.2, C14.2, CN1.GND, CR1220.-, FIX.C, GND@1.1, GND@2.1, GND@3.1, GND@4.1, GND@5.1, GND@6.1, GRN.C, IC1.1 (GND), IC2.3 (GND), IC2.EXP (GND), IC2.M (GND), ORNG.C, R1.1, R6.1, U1.2 (COMMON_ANODE), U2.P$3 (GND), U2.P$8 (GND), U2.P$12 (GND), U2.P$19 (GND), U$1.P$8 (VSSA), U$1.P$23 (VSS), U$1.P$35 (VSS), U$1.P$47 (VSS), U$2.2 (GND), U$2.5 (WP), U$3.2
GPS_IN: GPS.1, U2.P$9 (TX), U$1.P$31 (PA10)
GREEN_LED: R3.2, U$1.P$27 (PB14)
HOST_RX: IC2.25 (RXD), OUT.1, U$1.P$21 (PB10)
HOST_TX: IC2.26 (TXD), IN.1, U$1.P$22 (PB11)
I2C_SCL: R9.1, U$1.P$42 (PB6), U$2.1 (SCL)
I2C_SDA: R10.1, U$1.P$43 (PB7), U$2.3 (SDA)
unnamed: SDN2.1, U$1.P$45 (PB8)
unnamed: P3_1.1, U$1.P$11 (PA1)
unnamed: C10.1, IC1.2 (VO), L1.1
unnamed: R1.2, U$1.P$44 (BOOT0)
unnamed: SWC.1, U$1.P$37 (PA14)
unnamed: SDN1.1, U$1.P$13 (PA3)
unnamed: SWD.1, U$1.P$34 (PA13)
unnamed: IRQ1.1, U$1.P$39 (PB3)
unnamed: C2.2, U$1.P$5 (OSC_IN), X1.P$2
unnamed: CS1.1, U$1.P$14 (PA4)
unnamed: IRQ2.1, U$1.P$40 (PB4)
unnamed: FIX.A, R8.1
unnamed: CS2.1, U$1.P$19 (PB1)
unnamed: DBG.1, U$1.P$12 (PA2)
unnamed: P3_2.1, U$1.P$46 (PB9)
unnamed: R2.1, RED.A
unnamed: ORNG.A, R3.1
unnamed: C1.1, U$1.P$6 (OSC_OUT), X1.P$1
unnamed: BLU.A, R4.1
unnamed: CTX.1, U$1.P$29 (PA8)
unnamed: IC2.9 (!RST), R5.2
unnamed: IC2.11 (!SUSPEND), R6.2
unnamed: GRN.A, R7.1
unnamed: BYP.1, U$1.P$30 (PA9)
unnamed: R8.2, U2.P$5 (3D-FIX)
unnamed: CR1220.+$2 (+1), U2.P$4 (VBACKUP)
ORANGE_LED: R7.2, U$1.P$26 (PB13)
P1_1: P1_1.1, U$1.P$20 (PB2)
P1_2: P1_2.1, U$1.P$2 (PC13)
PPS: PPS.1, U2.P$13 (1PPS), U$1.P$10 (PA0)
PWR: RED.C
SDI: SDI1.1, SDI2.1, U$1.P$17 (PA7)
SDO: SDO1.1, SDO2.1, U$1.P$16 (PA6)
SPI_CLK: CLK1.1, CLK2.1, U$1.P$15 (PA5)
USBM: CN1.D-, IC2.5 (D-), U1.1 (CATHODE_2)
USBP: CN1.D+, IC2.4 (D+), U1.3 (CATHODE_3)
VDD1: C13.1, C14.1, L8.2, U2.P$1 (VCC)

Notes on the sheet:
Peter Antypas

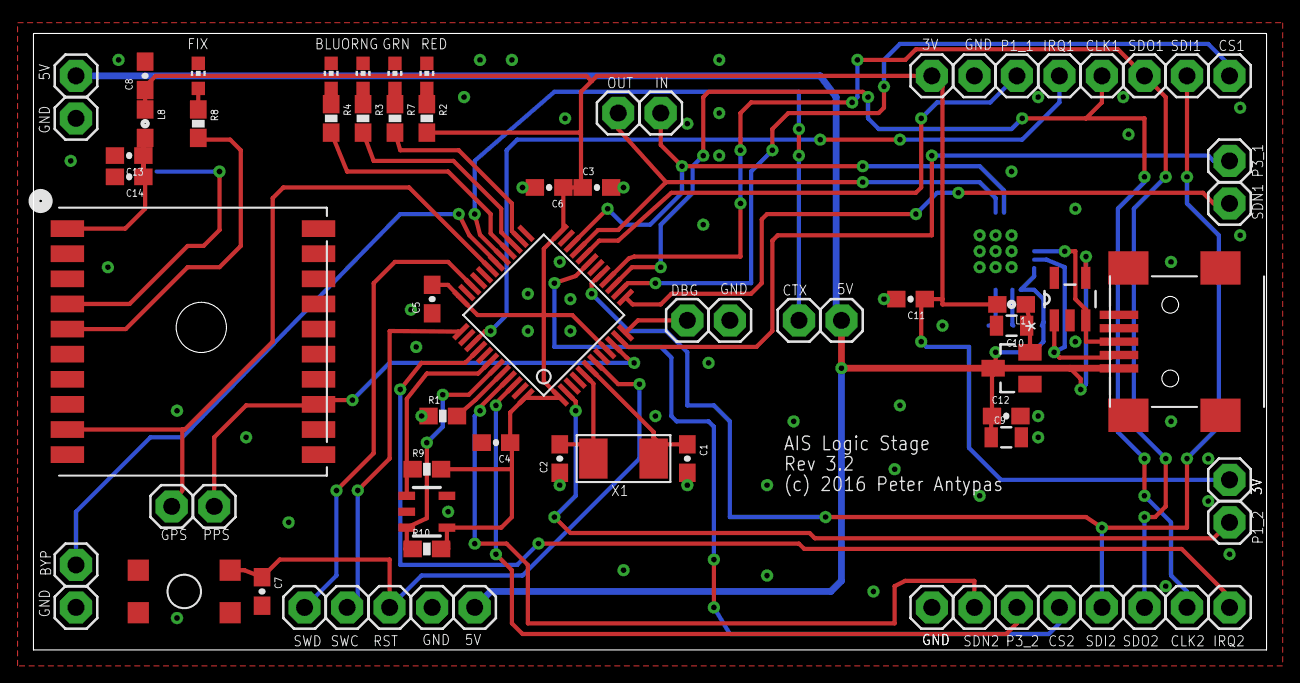
[picture p214: board logic.brd from above]

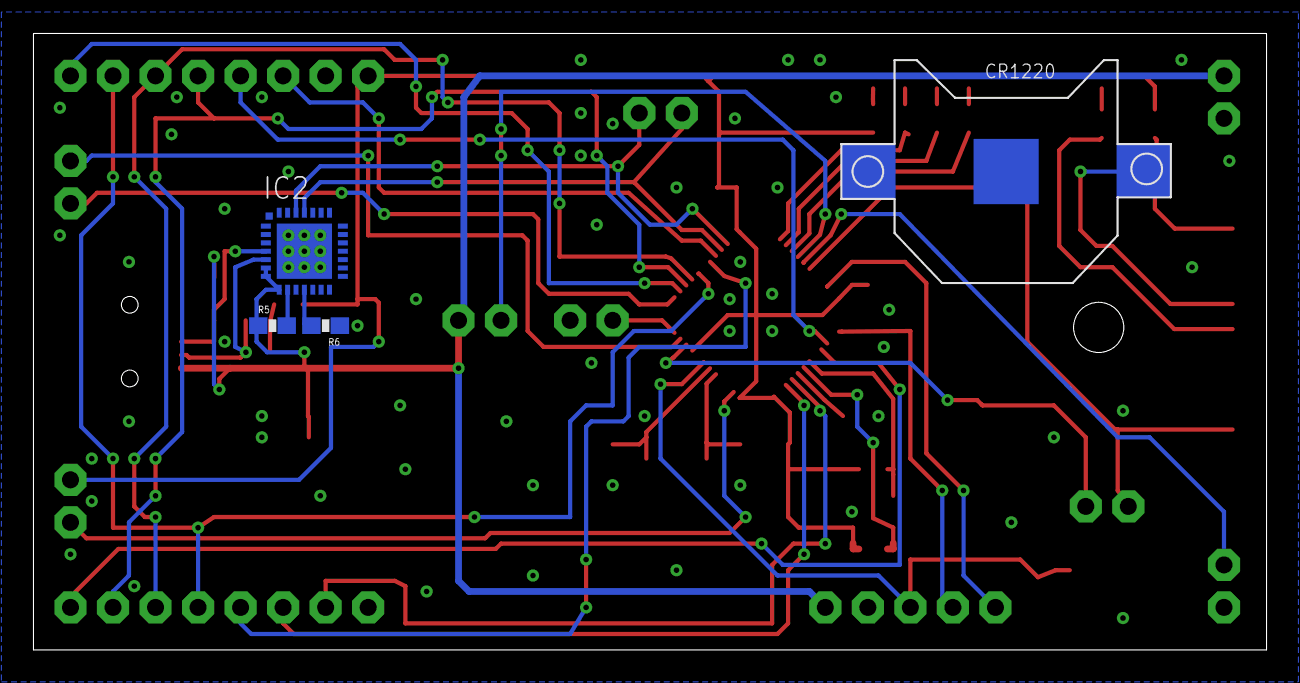
[picture p215: board logic.brd from below]

Board: 2 copper layers, 73.6 x 36.8 mm, 78 parts (4 on the bottom side), 47 nets.
