peterantypas/maiana/eagle/rf.brd

## EAGLE design legacy/eagle/rf.brd (2016-05-29, an earlier design)

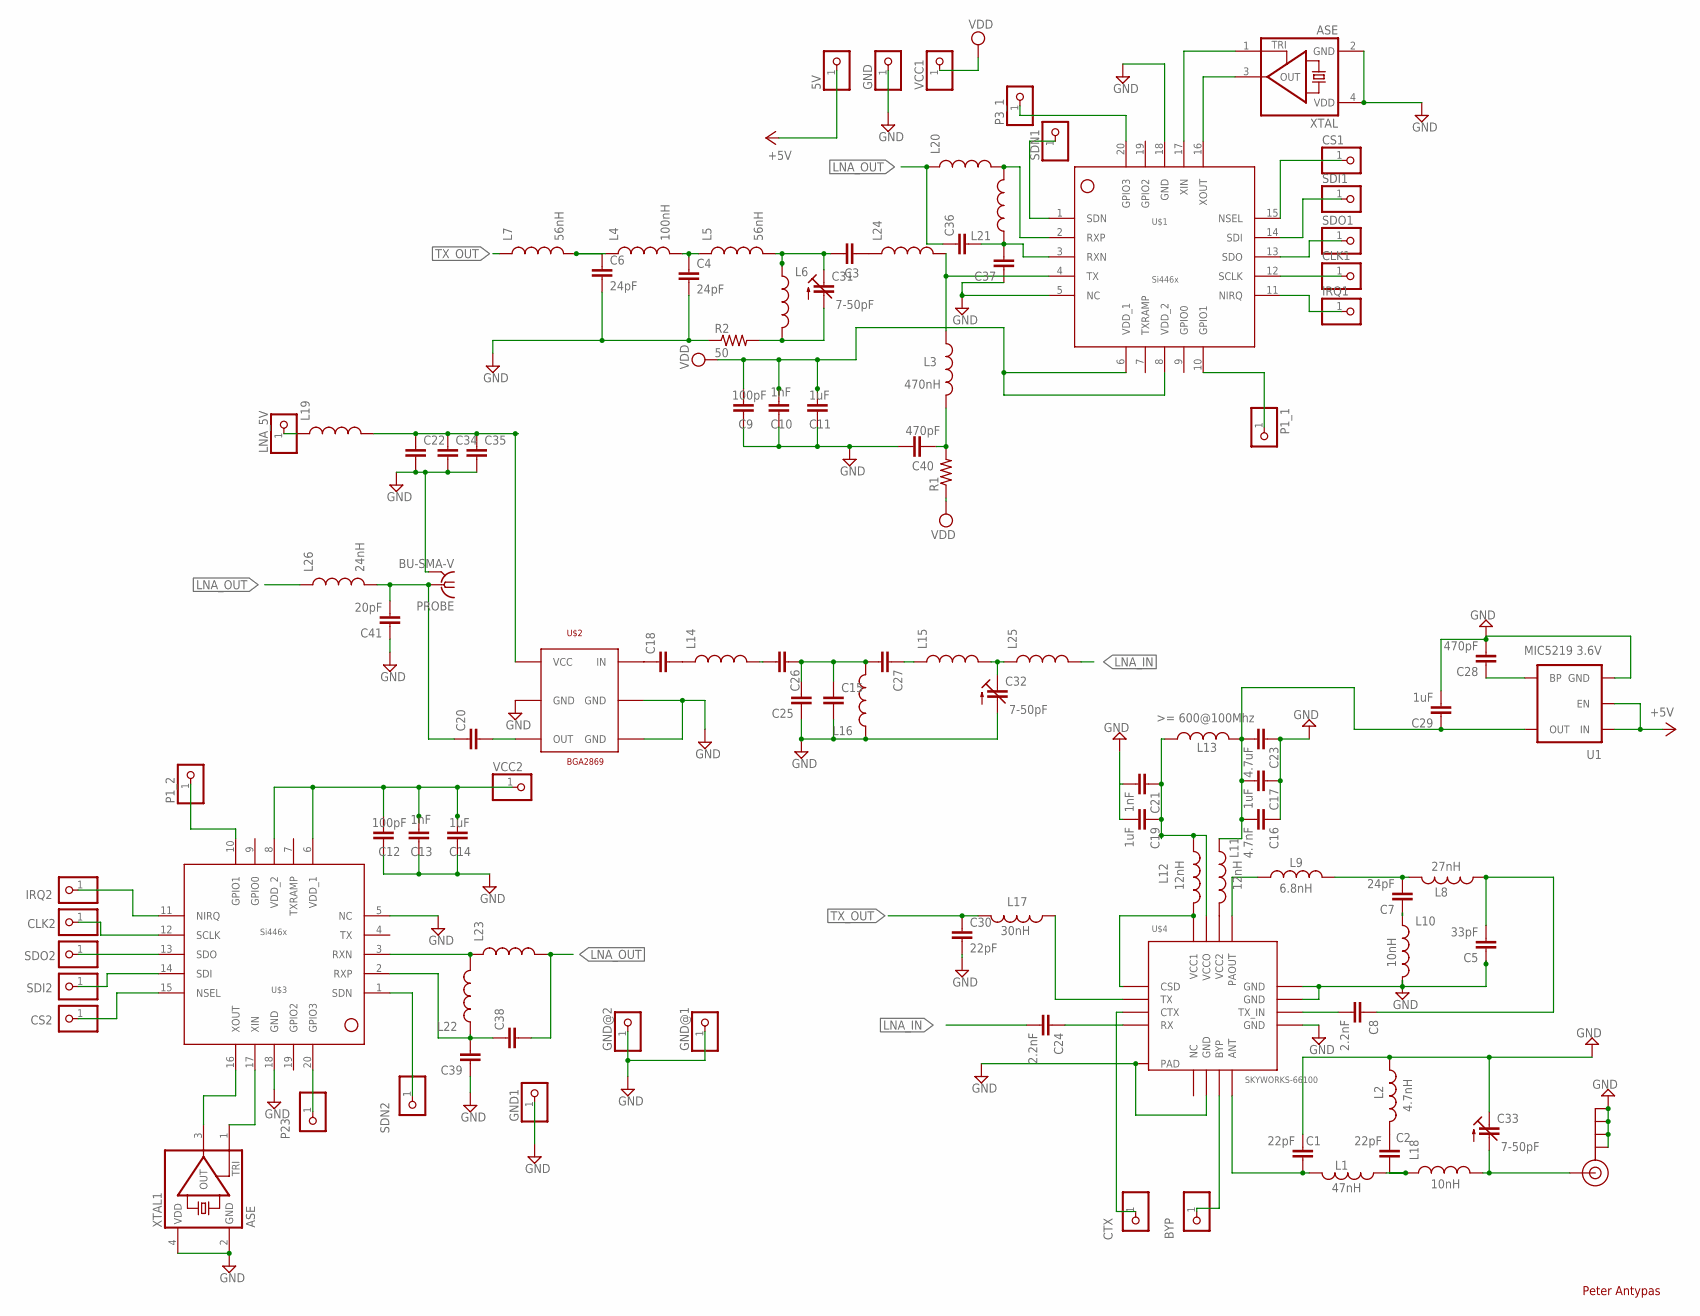
[picture p216: schematic rf.sch]

Parts:
5V: PINHD-1X1; 1X01
BYP: PINHD-1X1; 1X01
C1, C2, C30: 22pF; 0603-CAP
C3, C15, C22, C25, C26, C27, C34, C35, C36, C37, C38, C39: CAP0603-CAP; 0603-CAP
C4, C6, C7: 24pF; 0603-CAP
C5: 33pF; 0603-CAP
C8: 2.2nF; 0603-CAP
C9, C12: 100pF; 0603-CAP
C10, C13: 1nF; 0603-CAP
C11, C14: 1uF; 0603-CAP
C16: 4.7nF; 0805
C17, C19, C29: 1uF; 0805
C18, C20: CAP0805; 0805
C21: 1nF; 0805
C23: 4.7uF; 0805
C24: 2.2nF; 0805
C28, C40: 470pF; 0603-CAP
C31, C32, C33: 7-50pF; CTRIMTZBX4
C41: 20pF; 0603-CAP
CLK1, CLK2: PINHD-1X1; 1X01
CS1, CS2: PINHD-1X1; 1X01
CTX: PINHD-1X1; 1X01
GND, GND1: PINHD-1X1; 1X01
GND@1, GND@2: PINHD-1X1; 1X01
IRQ1, IRQ2: PINHD-1X1; 1X01
J$1: SMA_EDGE; SMA-EDGE
L1: 47nH; 0603
L2: 4.7nH; 0603
L3: 470nH; 0805
L4: 100nH; 0603
L5, L7: 56nH; 0603
L6, L14, L15, L16, L19, L20, L21, L22, L23, L24, L25: INDUCTOR30OHM,1.8A; 0603
L8: 27nH; 0603
L9: 6.8nH; 0603
L10, L18: 10nH; 0603
L11, L12: 12nH; 0603
L13: >= 600@100Mhz; 0603
L17: 30nH; 0603
L26: 24nH; 0603
LNA_5V: PINHD-1X1; 1X01
P1_1, P1_2, P3_1, P23: PINHD-1X1; 1X01
PROBE: BU-SMA-V
R1: RESISTOR0603-RES; 0603-RES
R2: 50; 0603-RES
SDI1, SDI2: PINHD-1X1; 1X01
SDN1, SDN2: PINHD-1X1; 1X01
SDO1, SDO2: PINHD-1X1; 1X01
U1: MIC5219 3.6V; SOT23-5
U$1, U$3: SI4463
U$2: BGA2869; SOT363
U$4: SKYWORKS-66100; MCM16
VCC1, VCC2: PINHD-1X1; 1X01
XTAL, XTAL1: ASE

Connections:
+5V: 5V.1, U1.1 (IN), U1.3 (EN)
CS: CS1.1, U$1.15 (NSEL)
GND: C1.2, C4.2, C5.1, C6.2, C9.2, C10.2, C11.2, C12.2, C13.2, C14.2, C15.2, C16.1, C17.1, C19.2, C21.2, C22.2, C23.1, C25.1, C28.2, C29.2, C30.2, C32.2 (A), C33.1 (E), C34.2, C35.2, C37.1, C39.1, C40.2, C41.1, GND.1, GND1.1, GND@1.1, GND@2.1, J$1.GND@0 (GND), J$1.GND@1 (GND), J$1.GND@2 (GND), J$1.GND@3 (GND), L2.1, L10.2, L16.1, PROBE.2, PROBE.3 (2), PROBE.4 (2), PROBE.5 (2), R2.1, U1.2 (GND), U$1.5 (NC), U$1.18 (GND), U$2.2 (GND), U$2.4 (GND), U$2.5 (GND), U$3.5 (NC), U$3.18 (GND), U$4.P$6 (GND), U$4.P$9 (GND), U$4.P$11 (GND), U$4.P$12 (GND), U$4.P$17 (PAD), XTAL.2 (GND), XTAL.4 (VDD), XTAL1.2 (GND), XTAL1.4 (VDD)
IRQ2: IRQ2.1, U$3.11 (NIRQ)
LNA_5V: C22.1, C34.1, C35.1, L19.2, U$2.1 (VCC)
LNA_IN: C24.2, L25.2
LNA_OUT: C36.1, C38.2, L20.1, L23.2, L26.1
unnamed: C2.1, L1.1, L18.1
unnamed: C1.1, L1.2, U$4.P$8 (ANT)
unnamed: C4.1, L4.2, L5.1
unnamed: C6.1, L4.1, L7.2
unnamed: P23.1, U$3.20 (GPIO3)
unnamed: L3.1, L24.2, U$1.4 (TX)
unnamed: U$1.17 (XIN), XTAL.1 (TRI)
unnamed: C2.2, L2.2
unnamed: C8.2, U$4.P$10 (TX_IN)
unnamed: P1_2.1, U$3.10 (GPIO1)
unnamed: C5.2, C8.1, L8.1
unnamed: C7.2, L8.2, L9.2
unnamed: U$1.16 (XOUT), XTAL.3 (OUT)
unnamed: C18.1, U$2.6 (IN)
unnamed: C18.2, L14.1
unnamed: C20.2, U$2.3 (OUT)
unnamed: C7.1, L10.1
unnamed: C31.2 (A), L6.2, R2.2
unnamed: L9.1, U$4.P$13 (PAOUT)
unnamed: C3.2, C31.1 (E), L5.2, L6.1
unnamed: C19.1, C21.1, L12.1, L13.1, U$4.P$15 (VCCO)
unnamed: L12.2, U$4.P$1 (CSD), U$4.P$16 (VCC1)
unnamed: C24.1, U$4.P$4 (RX)
unnamed: IRQ1.1, U$1.11 (NIRQ)
unnamed: BYP.1, U$4.P$7 (BYP)
unnamed: CTX.1, U$4.P$3 (CTX)
unnamed: C28.1, U1.4 (BP)
unnamed: C16.2, C17.2, C23.2, C29.1, L11.1, L13.2, U1.5 (OUT)
unnamed: SDI2.1, U$3.14 (SDI)
unnamed: CS2.1, U$3.15 (NSEL)
unnamed: L11.2, U$4.P$14 (VCC2)
unnamed: C15.1, C25.2, C26.1, C27.2, L16.2
unnamed: C27.1, L15.1
unnamed: C26.2, L14.2
unnamed: SDN1.1, U$1.1 (SDN)
unnamed: U$3.17 (XIN), XTAL1.1 (TRI)
unnamed: U$3.16 (XOUT), XTAL1.3 (OUT)
unnamed: SDN2.1, U$3.1 (SDN)
unnamed: SDO2.1, U$3.13 (SDO)
unnamed: L17.1, U$4.P$2 (TX)
unnamed: C33.2 (A), J$1.SIG (SIGNAL), L18.2
unnamed: CLK2.1, U$3.12 (SCLK)
unnamed: L19.1, LNA_5V.1
unnamed: L20.2, L21.2, U$1.2 (RXP)
unnamed: L22.2, L23.1, U$3.3 (RXN)
unnamed: C38.1, C39.2, L22.1, U$3.2 (RXP)
unnamed: C36.2, C37.2, L21.1, U$1.3 (RXN)
unnamed: C40.1, L3.2, R1.2
unnamed: C3.1, L24.1
unnamed: C32.1 (E), L15.2, L25.1
unnamed: C20.1, C41.2, L26.2, PROBE.1
SCLK: CLK1.1, U$1.12 (SCLK)
SCLK2: P1_1.1, U$1.10 (GPIO1)
SCLK3: P3_1.1, U$1.20 (GPIO3)
SDI: SDI1.1, U$1.14 (SDI)
SDO: SDO1.1, U$1.13 (SDO)
TX_OUT: C30.1, L7.1, L17.2
VCC2: C12.1, C13.1, C14.1, U$3.6 (VDD_1), U$3.8 (VDD_2), VCC2.1
VDD: C9.1, C10.1, C11.1, R1.1, U$1.6 (VDD_1), U$1.8 (VDD_2), VCC1.1

Notes on the sheet:
Peter Antypas

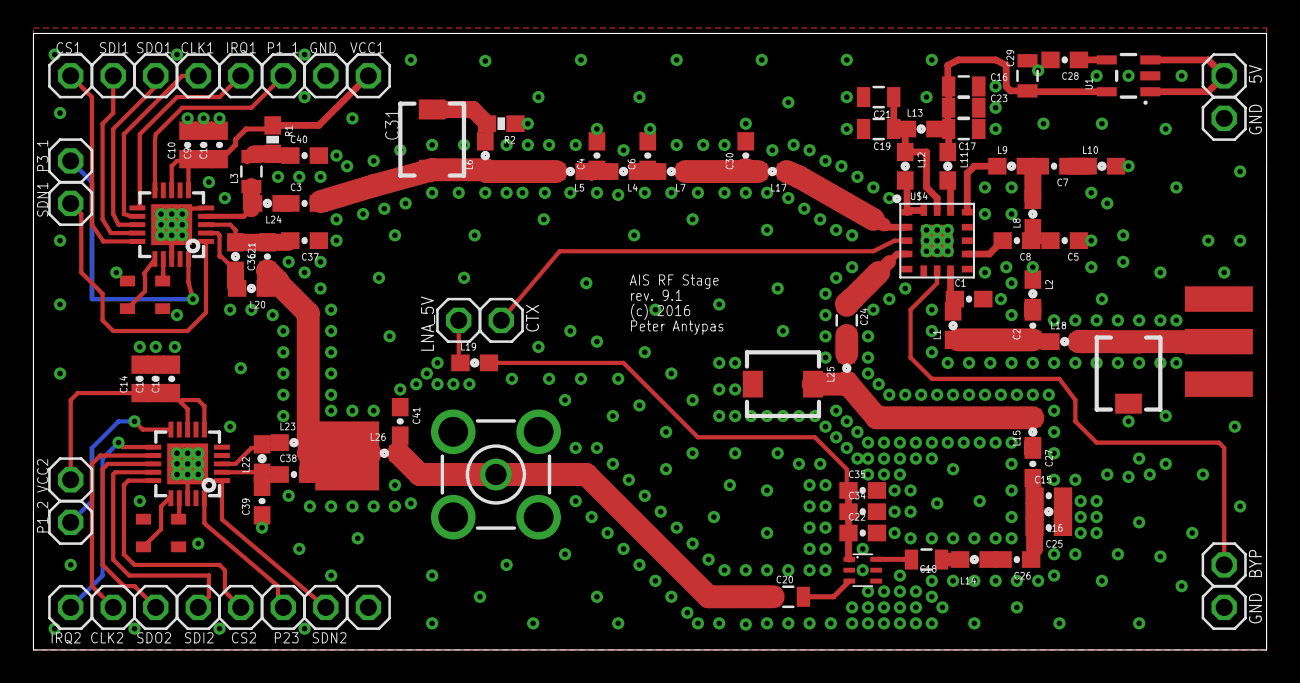
[picture p217: board rf.brd from above]

Board: 2 copper layers, 73.6 x 36.8 mm, 104 parts (0 on the bottom side), 66 nets.
