peterantypas/maiana/latest/Firmware/Transponder/Src/main.cpp

/*
  Copyright (c) 2016-2020 Peter Antypas

  This file is part of the MAIANA™ transponder firmware.

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
  You should have received a copy of the GNU General Public License
  along with this program.  If not, see <https://www.gnu.org/licenses/>
 */

#include "config.h"
#include "RadioManager.hpp"
#include "RXPacketProcessor.hpp"
#include "DataTerminal.hpp"
#include "TXScheduler.hpp"
#include "GPS.hpp"
#include "LEDManager.hpp"
#include "CommandProcessor.hpp"
#include "bsp.hpp"


void jump_to_bootloader()
{
  typedef void (*pFunction)(void);
  pFunction systemBootloader;

  /**
   * System bootloader for L4xx series resides at 0x1fff0000,
   * so the first 4 bytes contain the stack pointer and the next 4 contain the
   * program counter
   */
  systemBootloader = (pFunction) (*((uint32_t *)(0x1fff0004)));
  uint32_t *pp = (uint32_t*)0x1fff0000;
  uint32_t msp = *pp;
  __set_MSP(msp);

  // That's it, jump!
  systemBootloader();
}

void mainLoop()
{
  bool cliBootMode = *(uint32_t*)BOOTMODE_ADDRESS == CLI_FLAG_MAGIC;

  EventPool::instance().init();
  EventQueue::instance().init();
  Configuration::instance().init();
  DataTerminal::instance().init();
  CommandProcessor::instance().init();
  RXPacketProcessor packetProcessor;
  GPS::instance().init();
  TXPacketPool::instance().init();
  TXScheduler::instance().init();
  RadioManager::instance().init();
  LEDManager::instance().init();

  if ( !cliBootMode )
    {
      if ( RadioManager::instance().initialized() )
        {
          GPS::instance().enable();
          RadioManager::instance().start();
        }
    }
  else
    {
      DataTerminal::instance().write("\r\n\r\nCLI mode. Send the 'reboot' command or cycle power to exit.\r\n");
    }

  *(uint32_t*)BOOTMODE_ADDRESS = 0;

#if ENABLE_WDT
  bsp_start_wdt();
#endif
  while (1)
    {
      EventQueue::instance().dispatch();
#if ENABLE_WDT
      bsp_refresh_wdt();
#endif
      __WFI();
    }
}


int main(void)
{
  if ( *(uint32_t*)BOOTMODE_ADDRESS == DFU_FLAG_MAGIC )
    {
      *(uint32_t*)BOOTMODE_ADDRESS = 0;
      jump_to_bootloader();
    }

  // This is for debugging imprecise bus faults
  //*(uint8_t *)0xe000ed08 |= 2;

  bsp_hw_init();
  mainLoop();
  return 1;
}
